proboterror/HIDman_ZX/firmware/usbhost.c

#include <stdio.h>
#include <stdlib.h>
#include <string.h>
#include "type.h"
#include "ch559.h"
#include "system.h"
#include "defs.h"
#include "usbdef.h"
#include "usbhost.h"
#include "data.h"
#include "settings.h"
#include "andyalloc.h"
#include "keyboardled.h"
#include "parsedescriptor.h"
#include "ps2protocol.h"
#include "usbll.h"
#include "preset.h"

#include "custom_handlers.h"
#include "kempston_joy.h"

#define RECEIVE_BUFFER_LEN 512
UINT8X ReceiveDataBuffer[RECEIVE_BUFFER_LEN];

__xdata bool DumpReport = 0;

void DumpHex(uint8_t *buffa, uint16_t len)
{
	static __xdata uint16_t cnt;

	for (cnt = 0; cnt < len; cnt++)
	{
		DEBUGOUT("%02X ", buffa[cnt]);
		if ((cnt & 0x000F) == 0x000F)
			DEBUGOUT("\n");
	}

	DEBUGOUT("\n\n");
}


void InitInterface(INTERFACE* Interface)
{
	memset(Interface, 0, sizeof(INTERFACE));

	Interface->InterfaceClass = USB_DEV_CLASS_RESERVED;
	Interface->InterfaceProtocol = USB_PROTOCOL_NONE;
	Interface->ReportSize = 0;
	Interface->EndpointNum = 0;


	for (int j = 0; j < MAX_ENDPOINT_NUM; j++)
	{
		Interface->Endpoint[j].EndpointAddr = 0;
		Interface->Endpoint[j].MaxPacketSize = 0;
		Interface->Endpoint[j].EndpointDir = ENDPOINT_IN;
		Interface->Endpoint[j].TOG = FALSE;
	}

	Interface->usesReports = 0;
}


void FillSetupReq(USB_SETUP_REQ *pSetupReq, UINT8 type, UINT8 req, UINT16 value, UINT16 index, UINT16 length)
{
	pSetupReq->bRequestType = type;
	pSetupReq->bRequest = req;
	pSetupReq->wValueL = value & 0xff;
	pSetupReq->wValueH = (value >> 8) & 0xff;
	pSetupReq->wIndexL = index & 0xff;
	pSetupReq->wIndexH = (index >> 8) & 0xff;
	pSetupReq->wLengthL = length & 0xff;
	pSetupReq->wLengthH = (length >> 8) & 0xff;
}

//-----------------------------------------------------------------------------------------
UINT8 GetDeviceDescr(USB_HUB_PORT *pUsbDevice, UINT8 *pDevDescr, UINT16 reqLen, UINT16 *pRetLen) //get device describtion
{
	static __xdata UINT8 s;
	static __xdata UINT16 len;

	static __xdata USB_SETUP_REQ SetupReq;
	FillSetupReq(&SetupReq, USB_REQ_TYP_IN | USB_REQ_TYP_STANDARD | USB_REQ_RECIP_DEVICE,
				 USB_GET_DESCRIPTOR, USB_DESCR_TYP_DEVICE << 8, 0, reqLen);

	s = HostCtrlTransfer(&SetupReq, pUsbDevice->MaxPacketSize0, pDevDescr, &len);

	if (s == ERR_SUCCESS)
	{
		if (pRetLen != NULL)
		{
			*pRetLen = len;
		}
	}

	return s;
}

//----------------------------------------------------------------------------------------
UINT8 GetConfigDescr(USB_HUB_PORT *pUsbDevice, UINT8 *pCfgDescr, UINT16 reqLen, UINT16 *pRetLen)
{
	static __xdata UINT8 s;
	static __xdata UINT16 len;

	static __xdata USB_SETUP_REQ SetupReq;
	FillSetupReq(&SetupReq, USB_REQ_TYP_IN | USB_REQ_TYP_STANDARD | USB_REQ_RECIP_DEVICE,
				 USB_GET_DESCRIPTOR, USB_DESCR_TYP_CONFIG << 8, 0, reqLen);
	s = HostCtrlTransfer(&SetupReq, pUsbDevice->MaxPacketSize0, pCfgDescr, &len);
	if (s == ERR_SUCCESS)
	{
		if (pRetLen != NULL)
		{
			*pRetLen = len;
		}
	}

	return s;
}

//-------------------------------------------------------------------------------------
UINT8 SetUsbAddress(USB_HUB_PORT *pUsbDevice, UINT8 addr)
{
	static __xdata UINT8 s;

	static __xdata USB_SETUP_REQ SetupReq;
	FillSetupReq(&SetupReq, USB_REQ_TYP_OUT | USB_REQ_TYP_STANDARD | USB_REQ_RECIP_DEVICE,
				 USB_SET_ADDRESS, addr, 0, 0);

	s = HostCtrlTransfer(&SetupReq, pUsbDevice->MaxPacketSize0, NULL, NULL);
	if (s == ERR_SUCCESS)
	{
		SetHostUsbAddr(addr);
	}

	return s;
}

//-------------------------------------------------------------------------------------
UINT8 SetUsbConfig(USB_HUB_PORT *pUsbDevice, UINT8 cfg)
{
	static __xdata UINT8 s;

	static __xdata USB_SETUP_REQ SetupReq;
	FillSetupReq(&SetupReq, USB_REQ_TYP_OUT | USB_REQ_TYP_STANDARD | USB_REQ_RECIP_DEVICE,
				 USB_SET_CONFIGURATION, cfg, 0, 0);

	s = HostCtrlTransfer(&SetupReq, pUsbDevice->MaxPacketSize0, NULL, NULL);

	return s;
}

//-----------------------------------------------------------------------------------------
UINT8 GetHubDescriptor(USB_HUB_PORT *pUsbDevice, UINT8 *pHubDescr, UINT16 reqLen, UINT16 *pRetLen)
{
	static __xdata UINT8 s;
	static __xdata UINT16 len;

	static __xdata USB_SETUP_REQ SetupReq;
	FillSetupReq(&SetupReq, USB_REQ_TYP_IN | USB_REQ_TYP_CLASS | USB_REQ_RECIP_DEVICE,
				 USB_GET_DESCRIPTOR, USB_DESCR_TYP_HUB << 8, 0, reqLen);
	s = HostCtrlTransfer(&SetupReq, pUsbDevice->MaxPacketSize0, (UINT8 *)pHubDescr, &len);

	if (s == ERR_SUCCESS)
	{
		if (pRetLen != NULL)
		{
			*pRetLen = len;
		}
	}

	return s;
}

//-----------------------------------------------------------------------------------------
UINT8 GetHubPortStatus(USB_HUB_PORT *pUsbDevice, UINT8 HubPort, UINT16 *pPortStatus, UINT16 *pPortChange)
{
	static __xdata UINT8 s;
	static __xdata UINT16 len;

	static __xdata UINT8 Ret[4];

	static __xdata USB_SETUP_REQ SetupReq;
	FillSetupReq(&SetupReq, USB_REQ_TYP_IN | USB_REQ_TYP_CLASS | USB_REQ_RECIP_OTHER,
				 USB_GET_STATUS, 0, HubPort, 4);

	s = HostCtrlTransfer(&SetupReq, pUsbDevice->MaxPacketSize0, Ret, &len);
	if (s == ERR_SUCCESS)
	{
		if (pPortStatus != NULL)
		{
			*pPortStatus = (Ret[1] << 8) | Ret[0];
		}

		if (pPortChange != NULL)
		{
			*pPortChange = (Ret[3] << 8) | Ret[2];
		}
	}

	return s;
}

//------------------------------------------------------------------------------------------
UINT8 SetHubPortFeature(USB_HUB_PORT *pUsbDevice, UINT8 HubPort, UINT8 selector) //this function set feature for port						//this funciton set
{
	static __xdata UINT8 s;

	static __xdata USB_SETUP_REQ SetupReq;
	FillSetupReq(&SetupReq, USB_REQ_TYP_OUT | USB_REQ_TYP_CLASS | USB_REQ_RECIP_OTHER,
				 USB_SET_FEATURE, selector, (0 << 8) | HubPort, 0);

	s = HostCtrlTransfer(&SetupReq, pUsbDevice->MaxPacketSize0, NULL, NULL);

	return s;
}

UINT8 ClearHubPortFeature(USB_HUB_PORT *pUsbDevice, UINT8 HubPort, UINT8 selector)
{
	static __xdata UINT8 s;

	static __xdata USB_SETUP_REQ SetupReq;
	FillSetupReq(&SetupReq, USB_REQ_TYP_OUT | USB_REQ_TYP_CLASS | USB_REQ_RECIP_OTHER,
				 USB_CLEAR_FEATURE, selector, (0 << 8) | HubPort, 0);

	s = HostCtrlTransfer(&SetupReq, pUsbDevice->MaxPacketSize0, NULL, NULL);

	return s;
}

//-----------------------------------------------------------------------------------------
UINT8 GetReportDescriptor(USB_HUB_PORT *pUsbDevice, UINT8 interface, UINT8 *pReportDescr, UINT16 reqLen, UINT16 *pRetLen)
{
	static __xdata UINT8 s;
	static __xdata UINT16 len;

	static __xdata USB_SETUP_REQ SetupReq;
	FillSetupReq(&SetupReq, USB_REQ_TYP_IN | USB_REQ_TYP_STANDARD | USB_REQ_RECIP_INTERF,
				 USB_GET_DESCRIPTOR, USB_DESCR_TYP_REPORT << 8, interface, reqLen);

	s = HostCtrlTransfer(&SetupReq, pUsbDevice->MaxPacketSize0, pReportDescr, &len);

	if (s == ERR_SUCCESS)
	{
		if (pRetLen != NULL)
		{
			*pRetLen = len;
		}
	}

	return s;
}

UINT8 SetBootProtocol(USB_HUB_PORT *pUsbDevice, UINT8 interface, uint16_t val)
{
	static __xdata UINT8 s;

	static __xdata USB_SETUP_REQ SetupReq;

	FillSetupReq(&SetupReq, 0b00100001, HID_SET_PROTOCOL, val, interface, 0);

	s = HostCtrlTransfer(&SetupReq, pUsbDevice->MaxPacketSize0, NULL, NULL);
	return s;
}

UINT8 GetBootProtocol(USB_HUB_PORT *pUsbDevice, UINT8 interface)
{
	static __xdata UINT8 s;
	static __xdata UINT8 ret;

	static __xdata USB_SETUP_REQ SetupReq;

	FillSetupReq(&SetupReq, 0b10100001, HID_GET_PROTOCOL, 0, interface, 1);

	s = HostCtrlTransfer(&SetupReq, pUsbDevice->MaxPacketSize0, &ret, NULL);

	return ret;
}

//-----------------------------------------------------------------------------------------
UINT8 SetIdle(USB_HUB_PORT *pUsbDevice, UINT16 durationMs, UINT8 reportID, UINT8 interface)
{
	static __xdata UINT8 s;

	static __xdata USB_SETUP_REQ SetupReq;
	UINT8 duration = (UINT8)(durationMs / 4);

	FillSetupReq(&SetupReq, USB_REQ_TYP_OUT | USB_REQ_TYP_CLASS | USB_REQ_RECIP_INTERF,
				 HID_SET_IDLE, (duration << 8) | reportID, interface, 0);

	s = HostCtrlTransfer(&SetupReq, pUsbDevice->MaxPacketSize0, NULL, NULL);

	return s;
}

//-----------------------------------------------------------------------------------------------
UINT8 SetReport(USB_HUB_PORT *pUsbDevice, UINT8 interface, UINT8 *pReport, UINT16 ReportLen)
{
	static __xdata UINT8 s;
	static __xdata UINT16 len;

	static __xdata USB_SETUP_REQ SetupReq;
	FillSetupReq(&SetupReq, USB_REQ_TYP_OUT | USB_REQ_TYP_CLASS | USB_REQ_RECIP_INTERF,
				 HID_SET_REPORT, HID_REPORT_OUTPUT << 8, interface, ReportLen);

	s = HostCtrlTransfer(&SetupReq, pUsbDevice->MaxPacketSize0, pReport, &len);

	return s;
}

//-----------------------------------------------------------------------------------------------
void InitUsbData(void)
{
	static int i;

	for (i = 0; i < ROOT_HUB_PORT_NUM; i++)
	{
		InitRootHubPortData(i);
	}
}

//-------------------------------------------------------------------------------------------
UINT8 HIDDataTransferReceive(USB_HUB_PORT *pUsbDevice)
{
	static UINT8 s, p;
	static int i, j;
	static int interfaceNum;
	static int endpointNum;

	static UINT16 len;

	custom_handler_t* hahdler = (custom_handler_t*)pUsbDevice->UserData;
	
	if (hahdler)
	{
		uint8_t gamepad_state = 0;

		if (hahdler->poll(pUsbDevice, &gamepad_state))
		{
			kempston_joy_set(gamepad_state);

			if(gamepad_state)
				setLED(false);
		}

		return ERR_SUCCESS;
	}

	s = 0;
	interfaceNum = pUsbDevice->InterfaceNum;
	for (i = 0; i < interfaceNum; i++)
	{
		//INTERFACE *pInterface = &pUsbDevice->Interface[i];
		__xdata INTERFACE *pInterface = (__xdata INTERFACE *)ListGetData(pUsbDevice->Interfaces, i);
		if (pInterface != NULL && pInterface->InterfaceClass == USB_DEV_CLASS_HID)
		{
			endpointNum = pInterface->EndpointNum;
			for (j = 0; j < endpointNum; j++)
			{
				ENDPOINT *pEndPoint = &pInterface->Endpoint[j];
				if (pEndPoint->EndpointDir == ENDPOINT_IN)
				{
					s = TransferReceive(pEndPoint, ReceiveDataBuffer, &len, 0);
					if (s == ERR_SUCCESS)
					{
						//TRACE1("interface %d data:", (UINT16)i);
						// HIS IS WHERE THE FUN STUFF GOES
						//ProcessHIDData(pInterface, ReceiveDataBuffer, len);
						ParseReport(pInterface, len * 8, ReceiveDataBuffer);
						if (HMSettings.SerialDebugOutput) {
							DEBUGOUT("I%hX L%X- ", i, len);
							DumpHex(ReceiveDataBuffer, len);
						}
					}
				}
			}
		}
	}

	return (s);
}

//enum device
BOOL EnumerateHubPort(__xdata USB_HUB_PORT *pUsbHubPort, UINT8 addr)
{
	static __xdata UINT8 s;
	static __xdata UINT16 len;
	static __xdata UINT16 cfgDescLen;

	static __xdata USB_HUB_PORT *pUsbDevice;
	static __xdata USB_CFG_DESCR *pCfgDescr;

	pUsbDevice = pUsbHubPort;

	//get first 8 bytes of device descriptor to get maxpacketsize0
	s = GetDeviceDescr(pUsbDevice, ReceiveDataBuffer, 8, &len);

	if (s != ERR_SUCCESS)
	{
		DEBUGOUT("gdd.fail\n");
		return (FALSE);
	}

	DEBUGOUT("gdd len:%d\n", len);

	ParseDeviceDescriptor((USB_DEV_DESCR *)ReceiveDataBuffer, len, pUsbDevice);

	DEBUGOUT("mps %d\n", pUsbDevice->MaxPacketSize0);

	//set device address
	s = SetUsbAddress(pUsbDevice, addr);
	if (s != ERR_SUCCESS)
	{
		DEBUGOUT("addr fail\n");
		return (FALSE);
	}

	DEBUGOUT("addr ok %d\n", pUsbDevice->DeviceAddress);
	pUsbDevice->DeviceAddress = addr;
	//get full bytes of device descriptor
	s = GetDeviceDescr(pUsbDevice, ReceiveDataBuffer, sizeof(USB_DEV_DESCR), &len);

	if (s != ERR_SUCCESS)
	{
		DEBUGOUT("gddfull fail\n");
		return (FALSE);
	}

	DEBUGOUT("gddfull ok %d\n", len);

	DEBUGOUT("Device Descriptor :\n")
	DumpHex(ReceiveDataBuffer, len);

	ParseDeviceDescriptor((USB_DEV_DESCR *)ReceiveDataBuffer, len, pUsbDevice);

	DEBUGOUT("0x%04X 0x%04X 0x%04X\n", pUsbDevice->VendorID, pUsbDevice->ProductID, pUsbDevice->bcdDevice);

	//get configure descriptor for the first time
	cfgDescLen = sizeof(USB_CFG_DESCR);

	s = GetConfigDescr(pUsbDevice, ReceiveDataBuffer, cfgDescLen, &len);
	if (s != ERR_SUCCESS)
	{
		DEBUGOUT("gcd1 fail\n");
		return (FALSE);
	}

	//get configure descriptor for the second time
	pCfgDescr = (USB_CFG_DESCR *)ReceiveDataBuffer;
	cfgDescLen = pCfgDescr->wTotalLengthL | (pCfgDescr->wTotalLengthH << 8);
	if (cfgDescLen > RECEIVE_BUFFER_LEN)
	{
		cfgDescLen = RECEIVE_BUFFER_LEN;
	}

	s = GetConfigDescr(pUsbDevice, ReceiveDataBuffer, cfgDescLen, &len);
	if (s != ERR_SUCCESS)
	{
		DEBUGOUT("gcd 2 fail\n");
		return (FALSE);
	}

	DEBUGOUT("Config Descriptor :\n")
	DumpHex(ReceiveDataBuffer, len);

	custom_handler_t* handler = match(pUsbDevice->VendorID, pUsbDevice->ProductID);

	if (handler)
	{
		pUsbHubPort->UserData = (void*)handler;
		handler->init(pUsbDevice, (USB_CFG_DESCR *)ReceiveDataBuffer, len);

		return true;
	}

	//parse config descriptor
	ParseConfigDescriptor((USB_CFG_DESCR *)ReceiveDataBuffer, len, pUsbDevice);

	DEBUGOUT("gcd ok %d\n", len);

	//set config
	s = SetUsbConfig(pUsbDevice, ((USB_CFG_DESCR *)ReceiveDataBuffer)->bConfigurationValue);
	if (s != ERR_SUCCESS)
	{
		DEBUGOUT("suc fail\n");
		return (FALSE);
	}

	TRACE("SetUsbConfig OK\r\n");
	TRACE1("configure=%bd\r\n", ((USB_CFG_DESCR *)ReceiveDataBuffer)->bConfigurationValue);

	TRACE1("pUsbDevice->InterfaceNum=%d\r\n", (UINT16)pUsbDevice->InterfaceNum);

	return (TRUE);
}

UINT8 AssignUniqueAddress(UINT8 RootHubIndex, UINT8 HubPortIndex)
{
	static UINT8 address;
	if (HubPortIndex == EXHUB_PORT_NONE)
	{
		address = (MAX_EXHUB_PORT_NUM + 1) * RootHubIndex + 1;
	}
	else
	{
		address = (MAX_EXHUB_PORT_NUM + 1) * RootHubIndex + 1 + HubPortIndex + 1;
	}

	return address;
}

BOOL EnumerateRootHubPort(UINT8 port)
{
	static __xdata UINT8 i, s;
	static __xdata UINT16 len;

	static __xdata UINT8 retry;

	static __xdata UINT8 addr;
	retry = 0;
	/*if (RootHubPort[port].HubPortStatus != PORT_DEVICE_INSERT)
	{
		return FALSE;
	}*/

	TRACE1("enumerate port:%bd\r\n", port);

//	DisableRootHubPort(port);

//	mDelaymS(500);

	ResetRootHubPort(port);
//	mDelaymS(500);

#if 1
	for (i = 0, s = 0; i < 10; i++) // 等待USB设备复位后重新连接,100mS超时
	{
		EnableRootHubPort(port);

		mDelaymS(1);
	}

#else
	for (i = 0, s = 0; i < 100; i++) // 等待USB设备复位后重新连接,100mS超时
	{
		mDelaymS(1);
		if (EnableRootHubPort(port) == ERR_SUCCESS) // 使能ROOT-HUB端口
		{
			i = 0;
			s++; // 计时等待USB设备连接后稳定
			if (s > 10 * retry)
			{
				break; // 已经稳定连接15mS
			}
		}
	}

	TRACE1("i:%d\r\n", (UINT16)i);

	if (i) // 复位后设备没有连接
	{
		DisableRootHubPort(port);
		TRACE1("Disable root hub %1d# port because of disconnect\n", (UINT16)port);

		return (ERR_USB_DISCON);
	}
#endif

	mDelaymS(100);

	SelectHubPort(port, EXHUB_PORT_NONE);

	addr = AssignUniqueAddress(port, EXHUB_PORT_NONE);
	if (EnumerateHubPort(&RootHubPort[port], addr))
	{
		RootHubPort[port].HubPortStatus = PORT_DEVICE_ENUM_SUCCESS;

		TRACE("EnumerateHubPort success\r\n");

		

		//SelectHubPort(port, EXHUB_PORT_NONE);
		if (RootHubPort[port].DeviceClass == USB_DEV_CLASS_HUB)
		{
			DEBUGOUT("\nFound hub\n");

			//hub
			USB_HUB_DESCR *pHubDescr;

			UINT8 hubPortNum;
			UINT16 hubPortStatus, hubPortChange;
			USB_HUB_PORT *pUsbDevice = &RootHubPort[port];

			//hub
			s = GetHubDescriptor(pUsbDevice, ReceiveDataBuffer, sizeof(USB_HUB_DESCR), &len);
			if (s != ERR_SUCCESS)
			{
				DisableRootHubPort(port);

				RootHubPort[port].HubPortStatus = PORT_DEVICE_ENUM_FAILED;
				DEBUGOUT("hub desc err\n");
				return (FALSE);
			}

			TRACE("GetHubDescriptor OK\r\n");
			TRACE1("len=%d\r\n", len);

			pHubDescr = (USB_HUB_DESCR *)ReceiveDataBuffer;
			hubPortNum = pHubDescr->bNbrPorts;

			TRACE1("hubPortNum=%bd\r\n", hubPortNum);
			DEBUGOUT("%d port hub\n", hubPortNum);

			if (hubPortNum > MAX_EXHUB_PORT_NUM)
			{
				hubPortNum = MAX_EXHUB_PORT_NUM;
			}

			pUsbDevice->HubPortNum = hubPortNum;

			//supply power for each port
			for (i = 0; i < hubPortNum; i++)
			{
				s = SetHubPortFeature(pUsbDevice, i + 1, HUB_PORT_POWER);
				if (s != ERR_SUCCESS)
				{
					TRACE1("SetHubPortFeature %d failed\r\n", (UINT16)i);

					SubHubPort[port][i].HubPortStatus = PORT_DEVICE_ENUM_FAILED;

					continue;
				}

				TRACE("SetHubPortFeature OK\r\n");
			}

			

			/*
			for (i = 0; i < hubPortNum; i++)
            {
                s = ClearHubPortFeature(pUsbDevice, i + 1, HUB_C_PORT_CONNECTION );
                if ( s != ERR_SUCCESS )
                {
                    TRACE1("ClearHubPortFeature %d failed\r\n", (UINT16)i);

                    continue;
                }

                TRACE("ClearHubPortFeature OK\r\n");
            }
*/
			INTERFACE *pInterface = (INTERFACE *)ListGetData(pUsbDevice->Interfaces, 0);

			ENDPOINT *pEndPoint = &pInterface->Endpoint[0];

			// "new thing" means wait for a change bitmap before clearing ports
			// this is how other USB stacks seem to do it
			printf("Doing new thing - %x\n", pInterface->Endpoint[0].EndpointAddr);

			uint8_t newthing = 1;

			s = TransferReceive(pEndPoint, ReceiveDataBuffer, &len, 20000);

			

			if (s != ERR_SUCCESS){
				DEBUGOUT("new enum. failed\n");
				// if "new thing" failed just clear all ports without waiting
				// seems to be required for some hubs
				newthing = 0;
				//return FALSE;
			}

			uint8_t changebitmap = ReceiveDataBuffer[0];

			DEBUGOUT("new enum. %x\n", changebitmap);

			for (i = 0; i < hubPortNum; i++)
			{
				if (!newthing || (changebitmap & (1 << (i+1)))) {
					DEBUGOUT("checkn port %d\n", i);
					mDelaymS(50);

					SelectHubPort(port, EXHUB_PORT_NONE); //切换到hub地址

					s = GetHubPortStatus(pUsbDevice, i + 1, &hubPortStatus, &hubPortChange);
					if (s != ERR_SUCCESS)
					{
						SubHubPort[port][i].HubPortStatus = PORT_DEVICE_ENUM_FAILED;

						TRACE1("GetHubPortStatus port:%d failed\r\n", (UINT16)(i + 1));

						return FALSE;
					}

					DEBUGOUT("ps- 0x%02X pc- 0x%02X\n", hubPortStatus, hubPortChange);

					TRACE2("hubPortStatus:0x%02X,hubPortChange:0x%02X\r\n", hubPortStatus, hubPortChange);

					if ((hubPortStatus & 0x0001) && (hubPortChange & 0x0001))
					{
						//device attached
						TRACE1("hubPort=%d\r\n", (UINT16)i);

						TRACE("device attached\r\n");

						DEBUGOUT("port %d attached\n", i);

						s = ClearHubPortFeature(pUsbDevice, i + 1, HUB_C_PORT_CONNECTION);
						if (s != ERR_SUCCESS)
						{
							SubHubPort[port][i].HubPortStatus = PORT_DEVICE_ENUM_FAILED;
							TRACE("ClearHubPortFeature failed\r\n");

							return FALSE;
						}

						TRACE("ClearHubPortFeature OK\r\n");


						s = SetHubPortFeature(pUsbDevice, i + 1, HUB_PORT_RESET); //reset the port device
						if (s != ERR_SUCCESS)
						{
							SubHubPort[port][i].HubPortStatus = PORT_DEVICE_ENUM_FAILED;

							TRACE1("SetHubPortFeature port:%d failed\r\n", (UINT16)(i + 1));

							return FALSE;
						}

						mDelaymS(100);
						do
						{
							s = GetHubPortStatus(pUsbDevice, i + 1, &hubPortStatus, &hubPortChange);
							if (s != ERR_SUCCESS)
							{
								SubHubPort[port][i].HubPortStatus = PORT_DEVICE_ENUM_FAILED;

								TRACE1("GetHubPortStatus port:%d failed\r\n", (UINT16)(i + 1));

								return FALSE;
							}

							mDelaymS(20);
						} while (hubPortStatus & 0x0010);

						if ((hubPortChange & 0x10) == 0x10) //reset over success
						{
							TRACE("reset complete\r\n");

							if (hubPortStatus & 0x0200)
							{
								//speed low
								SubHubPort[port][i].DeviceSpeed = LOW_SPEED;
								DEBUGOUT("lowspeed\n");
								TRACE("low speed device\r\n");
							}
							else
							{
								//full speed device
								SubHubPort[port][i].DeviceSpeed = FULL_SPEED;
								DEBUGOUT("fullspeed\n");
								TRACE("full speed device\r\n");
							}

							s = ClearHubPortFeature(pUsbDevice, i + 1, HUB_C_PORT_RESET);
							if (s != ERR_SUCCESS)
							{
								TRACE("ClearHubPortFeature failed\r\n");
							}
							else
							{
								TRACE("ClearHubPortFeature OK\r\n");
							}

							/*s = ClearHubPortFeature(pUsbDevice, i + 1, HUB_PORT_SUSPEND);
							if (s != ERR_SUCCESS)
							{
								SubHubPort[port][i].HubPortStatus = PORT_DEVICE_ENUM_FAILED;
								TRACE("ClearHubPortFeature failed\r\n");

								return FALSE;
							}

							TRACE("ClearHubPortFeature OK\r\n");

							mDelaymS(500);*/

							SelectHubPort(port, i);

							addr = AssignUniqueAddress(port, i);
							if (EnumerateHubPort(&SubHubPort[port][i], addr))
							{
								DEBUGOUT("enum.OK\n");
								TRACE("EnumerateHubPort success\r\n");
								SubHubPort[port][i].HubPortStatus = PORT_DEVICE_ENUM_SUCCESS;
							}
							else
							{
								DEBUGOUT("enum.fail\n");
								TRACE("EnumerateHubPort failed\r\n");
								SubHubPort[port][i].HubPortStatus = PORT_DEVICE_ENUM_FAILED;
							}
						}
					}
				}
			}
		}
	}
	else
	{
		DisableRootHubPort(port);

		RootHubPort[port].HubPortStatus = PORT_DEVICE_ENUM_FAILED;
	}

	return TRUE;
}

UINT8 QueryHubPortAttach(void)
{
	static __xdata BOOL res;

	static __xdata UINT8 s;

	res = FALSE; s = ERR_SUCCESS;

	if (UIF_DETECT)
	{
		//plug in or plug out
		UIF_DETECT = 0;

		if (USB_HUB_ST & bUHS_H0_ATTACH)
		{
			//port 0 plug in
			if (RootHubPort[0].HubPortStatus == PORT_DEVICE_NONE
				/*|| (UHUB0_CTRL & bUH_PORT_EN) == 0x00*/)
			{
				DisableRootHubPort(0);

				RootHubPort[0].HubPortStatus = PORT_DEVICE_INSERT;

				s = ERR_USB_CONNECT;

				TRACE("hub 0 dev in\r\n");
			}
		}
		else if (RootHubPort[0].HubPortStatus >= PORT_DEVICE_INSERT)
		{
			DisableRootHubPort(0);

			if (s == ERR_SUCCESS)
			{
				s = ERR_USB_DISCON;
			}

			TRACE("hub 0 dev out\r\n");
		}

		if (USB_HUB_ST & bUHS_H1_ATTACH)
		{
			//port 1 plug in
			if (RootHubPort[1].HubPortStatus == PORT_DEVICE_NONE
				/*|| ( UHUB1_CTRL & bUH_PORT_EN ) == 0x00*/)
			{
				DisableRootHubPort(1);

				RootHubPort[1].HubPortStatus = PORT_DEVICE_INSERT;

				s = ERR_USB_CONNECT;

				TRACE("hub 1 dev in\r\n");
			}
		}
		else if (RootHubPort[1].HubPortStatus >= PORT_DEVICE_INSERT)
		{
			DisableRootHubPort(1);

			if (s == ERR_SUCCESS)
			{
				s = ERR_USB_DISCON;
			}

			TRACE("hub 1 dev out\r\n");
		}
	}

	return s;
}


void regrabinterfaces(__xdata USB_HUB_PORT *pUsbHubPort)
{
	static __xdata UINT8 i, s, c;
	static __xdata UINT16 len, cnt;
	static __xdata USB_HUB_PORT *pUsbDevice;

	pUsbDevice = pUsbHubPort;
	if (pUsbDevice->DeviceClass != USB_DEV_CLASS_HUB)
	{
		for (i = 0; i < pUsbDevice->InterfaceNum; i++)
		{
#ifdef DEBUG
			int j;
#endif

			DEBUGOUT("\n\n");
			//INTERFACE *pInterface = &pUsbDevice->Interface[i];		
			INTERFACE *pInterface = (INTERFACE *)ListGetData(pUsbDevice->Interfaces, i);

			TRACE1("InterfaceClass=0x%02X\r\n", (UINT16)pInterface->InterfaceClass);
			TRACE1("InterfaceProtocol=0x%02X\r\n", (UINT16)pInterface->InterfaceProtocol);

			if (pInterface->InterfaceClass == USB_DEV_CLASS_HID)
			{
				s = SetIdle(pUsbDevice, 0, 0, i);

				if (s != ERR_SUCCESS)
				{
					TRACE("SetIdle failed\r\n");
				}
				else
				{
					TRACE("SetIdle OK\r\n");
				}

				DEBUGOUT("Interface %x:\n", i);
				DEBUGOUT("InterfaceProtocol: %x\r\n", pInterface->InterfaceProtocol);

				TRACE1("Report Size:%d\r\n", pInterface->ReportSize);
				s = GetReportDescriptor(pUsbDevice, i, ReceiveDataBuffer, pInterface->ReportSize <= sizeof(ReceiveDataBuffer) ? pInterface->ReportSize : sizeof(ReceiveDataBuffer), &len);

				if (s != ERR_SUCCESS)
				{
					DEBUGOUT("rep descr fail %u\n", s);
					return; // FALSE;
				}

				TRACE("GetReportDescriptor OK\r\n");
				TRACE1("get report descr len:%d\r\n", len);

				DEBUGOUT("\n\nInterface %hx Report Descriptor - \n", i);
				DumpHex(ReceiveDataBuffer, len);



				// use default boot mode descriptors if a keyboard or mouse is detected and "advanced USB" is disabled in menu
				if (
					(!HMSettings.MouseReportMode && pInterface->InterfaceProtocol == HID_PROTOCOL_MOUSE) ||
					(!HMSettings.KeyboardReportMode && pInterface->InterfaceProtocol == HID_PROTOCOL_KEYBOARD)
					)
				{
					// if it supports boot mode, enable that and use the default descriptor
					if (pInterface->InterfaceSubClass == 0x01) {
						DEBUGOUT("set boot mode - %x - ", GetBootProtocol(pUsbDevice, i));
						SetBootProtocol(pUsbDevice, i, 0);
						ParseReportDescriptor(
							pInterface->InterfaceProtocol == HID_PROTOCOL_MOUSE ? StandardMouseDescriptor : StandardKeyboardDescriptor, 
							pInterface->InterfaceProtocol == HID_PROTOCOL_MOUSE ? 50 : 63, 
							pInterface
						);
						
						DEBUGOUT("%x\n", GetBootProtocol(pUsbDevice, i));
					}
					// Otherwise don't attempt to use this device at all unless advanced USB is enabled
					else{ 
						DEBUGOUT("No boot mode\n");
						continue;
					}
				}
				else {
					// only switch into report mode if boot mode is supported (yeah that's the way it works)
					if (pInterface->InterfaceSubClass == 0x01) {
						DEBUGOUT("set report mode - %x - ", GetBootProtocol(pUsbDevice, i));
						SetBootProtocol(pUsbDevice, i, 1);
						DEBUGOUT("%x\n", GetBootProtocol(pUsbDevice, i));
					}
					
					ParseReportDescriptor(ReceiveDataBuffer, len, pInterface);
					DumpHID(pInterface);
				}

				if (pInterface->InterfaceProtocol == HID_PROTOCOL_KEYBOARD)
				{
					UINT8 led;

					led = GetKeyboardLedStatus();
					SetReport(pUsbDevice, i, &led, sizeof(led));
					DEBUGOUT("SetReport\n");
				}
			}
		}
	}
}

void RegrabDeviceReports(UINT8 port)
{
	static __xdata USB_HUB_PORT *pUsbHubPort;
	pUsbHubPort = &RootHubPort[port];

	if (pUsbHubPort->HubPortStatus == PORT_DEVICE_ENUM_SUCCESS)
	{
		if (pUsbHubPort->DeviceClass != USB_DEV_CLASS_HUB)
		{
			SelectHubPort(port, EXHUB_PORT_NONE);
			regrabinterfaces(pUsbHubPort);
		}
		else
		{
			UINT8 exHubPortNum = pUsbHubPort->HubPortNum;
			UINT8 i;

			for (i = 0; i < exHubPortNum; i++)
			{
				pUsbHubPort = &SubHubPort[port][i];

				if (pUsbHubPort->HubPortStatus == PORT_DEVICE_ENUM_SUCCESS && pUsbHubPort->DeviceClass != USB_DEV_CLASS_HUB)
				{
					SelectHubPort(port, i);
					regrabinterfaces(pUsbHubPort);
				}
			}
		}
	}
}

void ReenumerateAllPorts(void){
	UINT8 i;
	
	DEBUGOUT("reenumerating all ports\n");
	mDelaymS(150);

	InitUsbData();
	andyclearmem();
	InitPresets();
	
	for (i = 0; i < ROOT_HUB_PORT_NUM; i++)
	{
		DEBUGOUT("port %d\n", i);

		EnumerateRootHubPort(i);
		RegrabDeviceReports(i);
	}
	DEBUGOUT("done reenumerating\n");
}

//----------------------------------------------------------------------------------
void DealUsbPort(void) //main function should use it at least 500ms
{
	static __xdata UINT8 s;

	s = QueryHubPortAttach();
	if (s == ERR_USB_CONNECT)
	{
		ReenumerateAllPorts();
	}
}

void InterruptProcessRootHubPort(UINT8 port)
{
	static __xdata USB_HUB_PORT *pUsbHubPort;
	pUsbHubPort = &RootHubPort[port];

	if (pUsbHubPort->HubPortStatus == PORT_DEVICE_ENUM_SUCCESS)
	{
		if (pUsbHubPort->DeviceClass != USB_DEV_CLASS_HUB)
		{
			SelectHubPort(port, EXHUB_PORT_NONE);

			HIDDataTransferReceive(pUsbHubPort);
			
		}
		else
		{
			UINT8 exHubPortNum = pUsbHubPort->HubPortNum;
			UINT8 i;

			for (i = 0; i < exHubPortNum; i++)
			{
				pUsbHubPort = &SubHubPort[port][i];

				if (pUsbHubPort->HubPortStatus == PORT_DEVICE_ENUM_SUCCESS && pUsbHubPort->DeviceClass != USB_DEV_CLASS_HUB)
				{
					SelectHubPort(port, i);
					HIDDataTransferReceive(pUsbHubPort);
				}
			}
		}
	}
}

void UpdateUsbKeyboardLedInternal(USB_HUB_PORT *pUsbDevice, UINT8 led)
{
	UINT8 i;
	for (i = 0; i < pUsbDevice->InterfaceNum; i++)
	{
		//INTERFACE *pInterface = &pUsbDevice->Interface[i];
		INTERFACE *pInterface = (INTERFACE *)ListGetData(pUsbDevice->Interfaces, i);
		if (pInterface->InterfaceClass == USB_DEV_CLASS_HID)
		{
			if (pInterface->InterfaceProtocol == HID_PROTOCOL_KEYBOARD)
			{
				SetReport(pUsbDevice, i, &led, 1);

				TRACE1("led=0x%x\r\n", led);
			}
		}
	}
}

//-----------------------------------------------------------------------------
void UpdateUsbKeyboardLed(UINT8 led)
{
	UINT8 i, j;

	for (i = 0; i < ROOT_HUB_PORT_NUM; i++)
	{
		USB_HUB_PORT *pUsbHubPort = &RootHubPort[i];
		if (pUsbHubPort->HubPortStatus == PORT_DEVICE_ENUM_SUCCESS)
		{
			if (pUsbHubPort->DeviceClass != USB_DEV_CLASS_HUB)
			{
				SelectHubPort(i, EXHUB_PORT_NONE);

				UpdateUsbKeyboardLedInternal(pUsbHubPort, led);
			}
			else
			{
				int exHubPortNum = pUsbHubPort->HubPortNum;

				for (j = 0; j < exHubPortNum; j++)
				{
					pUsbHubPort = &SubHubPort[i][j];

					if (pUsbHubPort->HubPortStatus == PORT_DEVICE_ENUM_SUCCESS && pUsbHubPort->DeviceClass != USB_DEV_CLASS_HUB)
					{
						SelectHubPort(i, j);

						UpdateUsbKeyboardLedInternal(pUsbHubPort, led);
					}
				}
			}
		}
	}
}

__xdata BOOL volatile s_CheckUsbPort0 = FALSE;
__xdata BOOL volatile s_CheckUsbPort1 = FALSE;

void ProcessUsbHostPort(void)
{	

	DealUsbPort();
	if (s_CheckUsbPort0)
	{
		s_CheckUsbPort0 = FALSE;
		
		InterruptProcessRootHubPort(0);
	}
	if (s_CheckUsbPort1)
	{
		s_CheckUsbPort1 = FALSE;

		InterruptProcessRootHubPort(1);
	}
}
