proboterror/HIDman_ZX/firmware/scancode.c

#include<stdio.h>
#ifndef __SDCC
#define __code
#endif
__code unsigned char KEY_SET2_PWR_MAKE[] = { 0x02, 0xE0, 0x37, };
__code unsigned char KEY_SET2_PWR_BREAK[] = { 0x03, 0xE0, 0xF0, 0x37, };

__code unsigned char KEY_SET2_SLEP_MAKE[] = { 0x02, 0xE0, 0x3F, };
__code unsigned char KEY_SET2_SLEP_BREAK[] = { 0x03, 0xE0, 0xF0, 0x3F, };

__code unsigned char KEY_SET2_WAKE_MAKE[] = { 0x02, 0xE0, 0x5E, };
__code unsigned char KEY_SET2_WAKE_BREAK[] = { 0x03, 0xE0, 0xF0, 0x5E, };

__code unsigned char KEY_SET2_A_MAKE[] = { 0x01, 0x1C, };
__code unsigned char KEY_SET2_A_BREAK[] = { 0x02, 0xF0, 0x1C, };

__code unsigned char KEY_SET2_B_MAKE[] = { 0x01, 0x32, };
__code unsigned char KEY_SET2_B_BREAK[] = { 0x02, 0xF0, 0x32, };

__code unsigned char KEY_SET2_C_MAKE[] = { 0x01, 0x21, };
__code unsigned char KEY_SET2_C_BREAK[] = { 0x02, 0xF0, 0x21, };

__code unsigned char KEY_SET2_D_MAKE[] = { 0x01, 0x23, };
__code unsigned char KEY_SET2_D_BREAK[] = { 0x02, 0xF0, 0x23, };

__code unsigned char KEY_SET2_E_MAKE[] = { 0x01, 0x24, };
__code unsigned char KEY_SET2_E_BREAK[] = { 0x02, 0xF0, 0x24, };

__code unsigned char KEY_SET2_F_MAKE[] = { 0x01, 0x2B, };
__code unsigned char KEY_SET2_F_BREAK[] = { 0x02, 0xF0, 0x2B, };

__code unsigned char KEY_SET2_G_MAKE[] = { 0x01, 0x34, };
__code unsigned char KEY_SET2_G_BREAK[] = { 0x02, 0xF0, 0x34, };

__code unsigned char KEY_SET2_H_MAKE[] = { 0x01, 0x33, };
__code unsigned char KEY_SET2_H_BREAK[] = { 0x02, 0xF0, 0x33, };

__code unsigned char KEY_SET2_I_MAKE[] = { 0x01, 0x43, };
__code unsigned char KEY_SET2_I_BREAK[] = { 0x02, 0xF0, 0x43, };

__code unsigned char KEY_SET2_J_MAKE[] = { 0x01, 0x3B, };
__code unsigned char KEY_SET2_J_BREAK[] = { 0x02, 0xF0, 0x3B, };

__code unsigned char KEY_SET2_K_MAKE[] = { 0x01, 0x42, };
__code unsigned char KEY_SET2_K_BREAK[] = { 0x02, 0xF0, 0x42, };

__code unsigned char KEY_SET2_L_MAKE[] = { 0x01, 0x4B, };
__code unsigned char KEY_SET2_L_BREAK[] = { 0x02, 0xF0, 0x4B, };

__code unsigned char KEY_SET2_M_MAKE[] = { 0x01, 0x3A, };
__code unsigned char KEY_SET2_M_BREAK[] = { 0x02, 0xF0, 0x3A, };

__code unsigned char KEY_SET2_N_MAKE[] = { 0x01, 0x31, };
__code unsigned char KEY_SET2_N_BREAK[] = { 0x02, 0xF0, 0x31, };

__code unsigned char KEY_SET2_O_MAKE[] = { 0x01, 0x44, };
__code unsigned char KEY_SET2_O_BREAK[] = { 0x02, 0xF0, 0x44, };

__code unsigned char KEY_SET2_P_MAKE[] = { 0x01, 0x4D, };
__code unsigned char KEY_SET2_P_BREAK[] = { 0x02, 0xF0, 0x4D, };

__code unsigned char KEY_SET2_Q_MAKE[] = { 0x01, 0x15, };
__code unsigned char KEY_SET2_Q_BREAK[] = { 0x02, 0xF0, 0x15, };

__code unsigned char KEY_SET2_R_MAKE[] = { 0x01, 0x2D, };
__code unsigned char KEY_SET2_R_BREAK[] = { 0x02, 0xF0, 0x2D, };

__code unsigned char KEY_SET2_S_MAKE[] = { 0x01, 0x1B, };
__code unsigned char KEY_SET2_S_BREAK[] = { 0x02, 0xF0, 0x1B, };

__code unsigned char KEY_SET2_T_MAKE[] = { 0x01, 0x2C, };
__code unsigned char KEY_SET2_T_BREAK[] = { 0x02, 0xF0, 0x2C, };

__code unsigned char KEY_SET2_U_MAKE[] = { 0x01, 0x3C, };
__code unsigned char KEY_SET2_U_BREAK[] = { 0x02, 0xF0, 0x3C, };

__code unsigned char KEY_SET2_V_MAKE[] = { 0x01, 0x2A, };
__code unsigned char KEY_SET2_V_BREAK[] = { 0x02, 0xF0, 0x2A, };

__code unsigned char KEY_SET2_W_MAKE[] = { 0x01, 0x1D, };
__code unsigned char KEY_SET2_W_BREAK[] = { 0x02, 0xF0, 0x1D, };

__code unsigned char KEY_SET2_X_MAKE[] = { 0x01, 0x22, };
__code unsigned char KEY_SET2_X_BREAK[] = { 0x02, 0xF0, 0x22, };

__code unsigned char KEY_SET2_Y_MAKE[] = { 0x01, 0x35, };
__code unsigned char KEY_SET2_Y_BREAK[] = { 0x02, 0xF0, 0x35, };

__code unsigned char KEY_SET2_Z_MAKE[] = { 0x01, 0x1A, };
__code unsigned char KEY_SET2_Z_BREAK[] = { 0x02, 0xF0, 0x1A, };

__code unsigned char KEY_SET2_1_MAKE[] = { 0x01, 0x16, };
__code unsigned char KEY_SET2_1_BREAK[] = { 0x02, 0xF0, 0x16, };

__code unsigned char KEY_SET2_2_MAKE[] = { 0x01, 0x1E, };
__code unsigned char KEY_SET2_2_BREAK[] = { 0x02, 0xF0, 0x1E, };

__code unsigned char KEY_SET2_3_MAKE[] = { 0x01, 0x26, };
__code unsigned char KEY_SET2_3_BREAK[] = { 0x02, 0xF0, 0x26, };

__code unsigned char KEY_SET2_4_MAKE[] = { 0x01, 0x25, };
__code unsigned char KEY_SET2_4_BREAK[] = { 0x02, 0xF0, 0x25, };

__code unsigned char KEY_SET2_5_MAKE[] = { 0x01, 0x2E, };
__code unsigned char KEY_SET2_5_BREAK[] = { 0x02, 0xF0, 0x2E, };

__code unsigned char KEY_SET2_6_MAKE[] = { 0x01, 0x36, };
__code unsigned char KEY_SET2_6_BREAK[] = { 0x02, 0xF0, 0x36, };

__code unsigned char KEY_SET2_7_MAKE[] = { 0x01, 0x3D, };
__code unsigned char KEY_SET2_7_BREAK[] = { 0x02, 0xF0, 0x3D, };

__code unsigned char KEY_SET2_8_MAKE[] = { 0x01, 0x3E, };
__code unsigned char KEY_SET2_8_BREAK[] = { 0x02, 0xF0, 0x3E, };

__code unsigned char KEY_SET2_9_MAKE[] = { 0x01, 0x46, };
__code unsigned char KEY_SET2_9_BREAK[] = { 0x02, 0xF0, 0x46, };

__code unsigned char KEY_SET2_0_MAKE[] = { 0x01, 0x45, };
__code unsigned char KEY_SET2_0_BREAK[] = { 0x02, 0xF0, 0x45, };

__code unsigned char KEY_SET2_ENTER_MAKE[] = { 0x01, 0x5A, };
__code unsigned char KEY_SET2_ENTER_BREAK[] = { 0x02, 0xF0, 0x5A, };

__code unsigned char KEY_SET2_ESCAPE_MAKE[] = { 0x01, 0x76, };
__code unsigned char KEY_SET2_ESCAPE_BREAK[] = { 0x02, 0xF0, 0x76, };

__code unsigned char KEY_SET2_BKSPACE_MAKE[] = { 0x01, 0x66, };
__code unsigned char KEY_SET2_BKSPACE_BREAK[] = { 0x02, 0xF0, 0x66, };

__code unsigned char KEY_SET2_TAB_MAKE[] = { 0x01, 0x0D, };
__code unsigned char KEY_SET2_TAB_BREAK[] = { 0x02, 0xF0, 0x0D, };

__code unsigned char KEY_SET2_SPACE_MAKE[] = { 0x01, 0x29, };
__code unsigned char KEY_SET2_SPACE_BREAK[] = { 0x02, 0xF0, 0x29, };

__code unsigned char KEY_SET2_DASH_MAKE[] = { 0x01, 0x4E, };
__code unsigned char KEY_SET2_DASH_BREAK[] = { 0x02, 0xF0, 0x4E, };

__code unsigned char KEY_SET2_EQUALS_MAKE[] = { 0x01, 0x55, };
__code unsigned char KEY_SET2_EQUALS_BREAK[] = { 0x02, 0xF0, 0x55, };

__code unsigned char KEY_SET2_LEFTSQB_MAKE[] = { 0x01, 0x54, };
__code unsigned char KEY_SET2_LEFTSQB_BREAK[] = { 0x02, 0xF0, 0x54, };

__code unsigned char KEY_SET2_RIGHTSQB_MAKE[] = { 0x01, 0x5B, };
__code unsigned char KEY_SET2_RIGHTSQB_BREAK[] = { 0x02, 0xF0, 0x5B, };

__code unsigned char KEY_SET2_BKSLASH_MAKE[] = { 0x01, 0x5D, };
__code unsigned char KEY_SET2_BKSLASH_BREAK[] = { 0x02, 0xF0, 0x5D, };

__code unsigned char KEY_SET2_EURO1_MAKE[] = { 0x01, 0x5D, };
__code unsigned char KEY_SET2_EURO1_BREAK[] = { 0x02, 0xF0, 0x5D, };

__code unsigned char KEY_SET2_SEMICOLON_MAKE[] = { 0x01, 0x4C, };
__code unsigned char KEY_SET2_SEMICOLON_BREAK[] = { 0x02, 0xF0, 0x4C, };

__code unsigned char KEY_SET2_APOSTROPHE_MAKE[] = { 0x01, 0x52, };
__code unsigned char KEY_SET2_APOSTROPHE_BREAK[] = { 0x02, 0xF0, 0x52, };

__code unsigned char KEY_SET2_TILDE_MAKE[] = { 0x01, 0x0E, };
__code unsigned char KEY_SET2_TILDE_BREAK[] = { 0x02, 0xF0, 0x0E, };

__code unsigned char KEY_SET2_COMMA_MAKE[] = { 0x01, 0x41, };
__code unsigned char KEY_SET2_COMMA_BREAK[] = { 0x02, 0xF0, 0x41, };

__code unsigned char KEY_SET2_PERIOD_MAKE[] = { 0x01, 0x49, };
__code unsigned char KEY_SET2_PERIOD_BREAK[] = { 0x02, 0xF0, 0x49, };

__code unsigned char KEY_SET2_FWSLASH_MAKE[] = { 0x01, 0x4A, };
__code unsigned char KEY_SET2_FWSLASH_BREAK[] = { 0x02, 0xF0, 0x4A, };

__code unsigned char KEY_SET2_CAPS_MAKE[] = { 0x01, 0x58, };
__code unsigned char KEY_SET2_CAPS_BREAK[] = { 0x02, 0xF0, 0x58, };

__code unsigned char KEY_SET2_F1_MAKE[] = { 0x01, 0x05, };
__code unsigned char KEY_SET2_F1_BREAK[] = { 0x02, 0xF0, 0x05, };

__code unsigned char KEY_SET2_F2_MAKE[] = { 0x01, 0x06, };
__code unsigned char KEY_SET2_F2_BREAK[] = { 0x02, 0xF0, 0x06, };

__code unsigned char KEY_SET2_F3_MAKE[] = { 0x01, 0x04, };
__code unsigned char KEY_SET2_F3_BREAK[] = { 0x02, 0xF0, 0x04, };

__code unsigned char KEY_SET2_F4_MAKE[] = { 0x01, 0x0C, };
__code unsigned char KEY_SET2_F4_BREAK[] = { 0x02, 0xF0, 0x0C, };

__code unsigned char KEY_SET2_F5_MAKE[] = { 0x01, 0x03, };
__code unsigned char KEY_SET2_F5_BREAK[] = { 0x02, 0xF0, 0x03, };

__code unsigned char KEY_SET2_F6_MAKE[] = { 0x01, 0x0B, };
__code unsigned char KEY_SET2_F6_BREAK[] = { 0x02, 0xF0, 0x0B, };

__code unsigned char KEY_SET2_F7_MAKE[] = { 0x01, 0x83, };
__code unsigned char KEY_SET2_F7_BREAK[] = { 0x02, 0xF0, 0x83, };

__code unsigned char KEY_SET2_F8_MAKE[] = { 0x01, 0x0A, };
__code unsigned char KEY_SET2_F8_BREAK[] = { 0x02, 0xF0, 0x0A, };

__code unsigned char KEY_SET2_F9_MAKE[] = { 0x01, 0x01, };
__code unsigned char KEY_SET2_F9_BREAK[] = { 0x02, 0xF0, 0x01, };

__code unsigned char KEY_SET2_F10_MAKE[] = { 0x01, 0x09, };
__code unsigned char KEY_SET2_F10_BREAK[] = { 0x02, 0xF0, 0x09, };

__code unsigned char KEY_SET2_F11_MAKE[] = { 0x01, 0x78, };
__code unsigned char KEY_SET2_F11_BREAK[] = { 0x02, 0xF0, 0x78, };

__code unsigned char KEY_SET2_F12_MAKE[] = { 0x01, 0x07, };
__code unsigned char KEY_SET2_F12_BREAK[] = { 0x02, 0xF0, 0x07, };

__code unsigned char KEY_SET2_PRTSCR_MAKE[] = { 0x02, 0xE0, 0x7C, };
__code unsigned char KEY_SET2_PRTSCR_BREAK[] = { 0x03, 0xE0, 0xF0, 0x7C, };

__code unsigned char KEY_SET2_SCRLOCK_MAKE[] = { 0x01, 0x7E, };
__code unsigned char KEY_SET2_SCRLOCK_BREAK[] = { 0x02, 0xF0, 0x7E, };

__code unsigned char KEY_SET2_PAUSE_MAKE[] = { 0x08, 0xE1, 0x14, 0x77, 0xE1, 0xF0, 0x14, 0xF0, 0x77, };
__code unsigned char KEY_SET2_INSERT_MAKE[] = { 0x02, 0xE0, 0x70, };
__code unsigned char KEY_SET2_INSERT_BREAK[] = { 0x03, 0xE0, 0xF0, 0x70, };

__code unsigned char KEY_SET2_HOME_MAKE[] = { 0x02, 0xE0, 0x6C, };
__code unsigned char KEY_SET2_HOME_BREAK[] = { 0x03, 0xE0, 0xF0, 0x6C, };

__code unsigned char KEY_SET2_PGUP_MAKE[] = { 0x02, 0xE0, 0x7D, };
__code unsigned char KEY_SET2_PGUP_BREAK[] = { 0x03, 0xE0, 0xF0, 0x7D, };

__code unsigned char KEY_SET2_DELETE_MAKE[] = { 0x02, 0xE0, 0x71, };
__code unsigned char KEY_SET2_DELETE_BREAK[] = { 0x03, 0xE0, 0xF0, 0x71, };

__code unsigned char KEY_SET2_END_MAKE[] = { 0x02, 0xE0, 0x69, };
__code unsigned char KEY_SET2_END_BREAK[] = { 0x03, 0xE0, 0xF0, 0x69, };

__code unsigned char KEY_SET2_PGDN_MAKE[] = { 0x02, 0xE0, 0x7A, };
__code unsigned char KEY_SET2_PGDN_BREAK[] = { 0x03, 0xE0, 0xF0, 0x7A, };

__code unsigned char KEY_SET2_RIGHT_MAKE[] = { 0x02, 0xE0, 0x74, };
__code unsigned char KEY_SET2_RIGHT_BREAK[] = { 0x03, 0xE0, 0xF0, 0x74, };

__code unsigned char KEY_SET2_LEFT_MAKE[] = { 0x02, 0xE0, 0x6B, };
__code unsigned char KEY_SET2_LEFT_BREAK[] = { 0x03, 0xE0, 0xF0, 0x6B, };

__code unsigned char KEY_SET2_DOWN_MAKE[] = { 0x02, 0xE0, 0x72, };
__code unsigned char KEY_SET2_DOWN_BREAK[] = { 0x03, 0xE0, 0xF0, 0x72, };

__code unsigned char KEY_SET2_UP_MAKE[] = { 0x02, 0xE0, 0x75, };
__code unsigned char KEY_SET2_UP_BREAK[] = { 0x03, 0xE0, 0xF0, 0x75, };

__code unsigned char KEY_SET2_NUMLCK_MAKE[] = { 0x01, 0x77, };
__code unsigned char KEY_SET2_NUMLCK_BREAK[] = { 0x02, 0xF0, 0x77, };

__code unsigned char KEY_SET2_PADFWSLASH_MAKE[] = { 0x02, 0xE0, 0x4A, };
__code unsigned char KEY_SET2_PADFWSLASH_BREAK[] = { 0x03, 0xE0, 0xF0, 0x4A, };

__code unsigned char KEY_SET2_PADASTERISK_MAKE[] = { 0x01, 0x7C, };
__code unsigned char KEY_SET2_PADASTERISK_BREAK[] = { 0x02, 0xF0, 0x7C, };

__code unsigned char KEY_SET2_PADMINUS_MAKE[] = { 0x01, 0x7B, };
__code unsigned char KEY_SET2_PADMINUS_BREAK[] = { 0x02, 0xF0, 0x7B, };

__code unsigned char KEY_SET2_PADPLUS_MAKE[] = { 0x01, 0x79, };
__code unsigned char KEY_SET2_PADPLUS_BREAK[] = { 0x02, 0xF0, 0x79, };

__code unsigned char KEY_SET2_PADENTER_MAKE[] = { 0x02, 0xE0, 0x5A, };
__code unsigned char KEY_SET2_PADENTER_BREAK[] = { 0x03, 0xE0, 0xF0, 0x5A, };

__code unsigned char KEY_SET2_PAD1_MAKE[] = { 0x01, 0x69, };
__code unsigned char KEY_SET2_PAD1_BREAK[] = { 0x02, 0xF0, 0x69, };

__code unsigned char KEY_SET2_PAD2_MAKE[] = { 0x01, 0x72, };
__code unsigned char KEY_SET2_PAD2_BREAK[] = { 0x02, 0xF0, 0x72, };

__code unsigned char KEY_SET2_PAD3_MAKE[] = { 0x01, 0x7A, };
__code unsigned char KEY_SET2_PAD3_BREAK[] = { 0x02, 0xF0, 0x7A, };

__code unsigned char KEY_SET2_PAD4_MAKE[] = { 0x01, 0x6B, };
__code unsigned char KEY_SET2_PAD4_BREAK[] = { 0x02, 0xF0, 0x6B, };

__code unsigned char KEY_SET2_PAD5_MAKE[] = { 0x01, 0x73, };
__code unsigned char KEY_SET2_PAD5_BREAK[] = { 0x02, 0xF0, 0x73, };

__code unsigned char KEY_SET2_PAD6_MAKE[] = { 0x01, 0x74, };
__code unsigned char KEY_SET2_PAD6_BREAK[] = { 0x02, 0xF0, 0x74, };

__code unsigned char KEY_SET2_PAD7_MAKE[] = { 0x01, 0x6C, };
__code unsigned char KEY_SET2_PAD7_BREAK[] = { 0x02, 0xF0, 0x6C, };

__code unsigned char KEY_SET2_PAD8_MAKE[] = { 0x01, 0x75, };
__code unsigned char KEY_SET2_PAD8_BREAK[] = { 0x02, 0xF0, 0x75, };

__code unsigned char KEY_SET2_PAD9_MAKE[] = { 0x01, 0x7D, };
__code unsigned char KEY_SET2_PAD9_BREAK[] = { 0x02, 0xF0, 0x7D, };

__code unsigned char KEY_SET2_PAD0_MAKE[] = { 0x01, 0x70, };
__code unsigned char KEY_SET2_PAD0_BREAK[] = { 0x02, 0xF0, 0x70, };

__code unsigned char KEY_SET2_PADPERIOD_MAKE[] = { 0x01, 0x71, };
__code unsigned char KEY_SET2_PADPERIOD_BREAK[] = { 0x02, 0xF0, 0x71, };

__code unsigned char KEY_SET2_EURO2_MAKE[] = { 0x01, 0x61, };
__code unsigned char KEY_SET2_EURO2_BREAK[] = { 0x02, 0xF0, 0x61, };

__code unsigned char KEY_SET2_APP_MAKE[] = { 0x02, 0xE0, 0x2F, };
__code unsigned char KEY_SET2_APP_BREAK[] = { 0x03, 0xE0, 0xF0, 0x2F, };

__code unsigned char KEY_SET2_KEYPOWER_MAKE[] = { 0x02, 0xE0, 0x37, };
__code unsigned char KEY_SET2_KEYPOWER_BREAK[] = { 0x03, 0xE0, 0xF0, 0x37, };

__code unsigned char KEY_SET2_PADEQUALS_MAKE[] = { 0x01, 0x0F, };
__code unsigned char KEY_SET2_PADEQUALS_BREAK[] = { 0x02, 0xF0, 0x0F, };

__code unsigned char KEY_SET2_F13_MAKE[] = { 0x01, 0x08, };
__code unsigned char KEY_SET2_F13_BREAK[] = { 0x02, 0xF0, 0x08, };

__code unsigned char KEY_SET2_F14_MAKE[] = { 0x01, 0x10, };
__code unsigned char KEY_SET2_F14_BREAK[] = { 0x02, 0xF0, 0x10, };

__code unsigned char KEY_SET2_F15_MAKE[] = { 0x01, 0x18, };
__code unsigned char KEY_SET2_F15_BREAK[] = { 0x02, 0xF0, 0x18, };

__code unsigned char KEY_SET2_F16_MAKE[] = { 0x01, 0x20, };
__code unsigned char KEY_SET2_F16_BREAK[] = { 0x02, 0xF0, 0x20, };

__code unsigned char KEY_SET2_F17_MAKE[] = { 0x01, 0x28, };
__code unsigned char KEY_SET2_F17_BREAK[] = { 0x02, 0xF0, 0x28, };

__code unsigned char KEY_SET2_F18_MAKE[] = { 0x01, 0x30, };
__code unsigned char KEY_SET2_F18_BREAK[] = { 0x02, 0xF0, 0x30, };

__code unsigned char KEY_SET2_F19_MAKE[] = { 0x01, 0x38, };
__code unsigned char KEY_SET2_F19_BREAK[] = { 0x02, 0xF0, 0x38, };

__code unsigned char KEY_SET2_F20_MAKE[] = { 0x01, 0x40, };
__code unsigned char KEY_SET2_F20_BREAK[] = { 0x02, 0xF0, 0x40, };

__code unsigned char KEY_SET2_F21_MAKE[] = { 0x01, 0x48, };
__code unsigned char KEY_SET2_F21_BREAK[] = { 0x02, 0xF0, 0x48, };

__code unsigned char KEY_SET2_F22_MAKE[] = { 0x01, 0x50, };
__code unsigned char KEY_SET2_F22_BREAK[] = { 0x02, 0xF0, 0x50, };

__code unsigned char KEY_SET2_F23_MAKE[] = { 0x01, 0x57, };
__code unsigned char KEY_SET2_F23_BREAK[] = { 0x02, 0xF0, 0x57, };

__code unsigned char KEY_SET2_F24_MAKE[] = { 0x01, 0x5F, };
__code unsigned char KEY_SET2_F24_BREAK[] = { 0x02, 0xF0, 0x5F, };

__code unsigned char KEY_SET2_PADCOMMA_MAKE[] = { 0x01, 0x6D, };
__code unsigned char KEY_SET2_PADCOMMA_BREAK[] = { 0x02, 0xF0, 0x6D, };

__code unsigned char KEY_SET2_INTL1_MAKE[] = { 0x01, 0x51, };
__code unsigned char KEY_SET2_INTL1_BREAK[] = { 0x02, 0xF0, 0x51, };

__code unsigned char KEY_SET2_INTL2_MAKE[] = { 0x01, 0x13, };
__code unsigned char KEY_SET2_INTL2_BREAK[] = { 0x02, 0xF0, 0x13, };

__code unsigned char KEY_SET2_INTL3_MAKE[] = { 0x01, 0x6A, };
__code unsigned char KEY_SET2_INTL3_BREAK[] = { 0x02, 0xF0, 0x6A, };

__code unsigned char KEY_SET2_INTL4_MAKE[] = { 0x01, 0x64, };
__code unsigned char KEY_SET2_INTL4_BREAK[] = { 0x02, 0xF0, 0x64, };

__code unsigned char KEY_SET2_INTL5_MAKE[] = { 0x01, 0x67, };
__code unsigned char KEY_SET2_INTL5_BREAK[] = { 0x02, 0xF0, 0x67, };

__code unsigned char KEY_SET2_INTL6_MAKE[] = { 0x01, 0x27, };
__code unsigned char KEY_SET2_INTL6_BREAK[] = { 0x02, 0xF0, 0x27, };

__code unsigned char KEY_SET2_LANG1_MAKE[] = { 0x01, 0xF2, };
__code unsigned char KEY_SET2_LANG2_MAKE[] = { 0x01, 0xF1, };
__code unsigned char KEY_SET2_LANG3_MAKE[] = { 0x01, 0x63, };
__code unsigned char KEY_SET2_LANG3_BREAK[] = { 0x02, 0xF0, 0x63, };

__code unsigned char KEY_SET2_LANG4_MAKE[] = { 0x01, 0x62, };
__code unsigned char KEY_SET2_LANG4_BREAK[] = { 0x02, 0xF0, 0x62, };

__code unsigned char KEY_SET2_LANG5_MAKE[] = { 0x01, 0x5F, };
__code unsigned char KEY_SET2_LANG5_BREAK[] = { 0x02, 0xF0, 0x5F, };

__code unsigned char KEY_SET2_LCTRL_MAKE[] = { 0x01, 0x14, };
__code unsigned char KEY_SET2_LCTRL_BREAK[] = { 0x02, 0xF0, 0x14, };

__code unsigned char KEY_SET2_LSHIFT_MAKE[] = { 0x01, 0x12, };
__code unsigned char KEY_SET2_LSHIFT_BREAK[] = { 0x02, 0xF0, 0x12, };

__code unsigned char KEY_SET2_LALT_MAKE[] = { 0x01, 0x11, };
__code unsigned char KEY_SET2_LALT_BREAK[] = { 0x02, 0xF0, 0x11, };

__code unsigned char KEY_SET2_LGUI_MAKE[] = { 0x02, 0xE0, 0x1F, };
__code unsigned char KEY_SET2_LGUI_BREAK[] = { 0x03, 0xE0, 0xF0, 0x1F, };

__code unsigned char KEY_SET2_RCTRL_MAKE[] = { 0x02, 0xE0, 0x14, };
__code unsigned char KEY_SET2_RCTRL_BREAK[] = { 0x03, 0xE0, 0xF0, 0x14, };

__code unsigned char KEY_SET2_RSHIFT_MAKE[] = { 0x01, 0x59, };
__code unsigned char KEY_SET2_RSHIFT_BREAK[] = { 0x02, 0xF0, 0x59, };

__code unsigned char KEY_SET2_RALT_MAKE[] = { 0x02, 0xE0, 0x11, };
__code unsigned char KEY_SET2_RALT_BREAK[] = { 0x03, 0xE0, 0xF0, 0x11, };

__code unsigned char KEY_SET2_RGUI_MAKE[] = { 0x02, 0xE0, 0x27, };
__code unsigned char KEY_SET2_RGUI_BREAK[] = { 0x03, 0xE0, 0xF0, 0x27, };

__code unsigned char KEY_SET2_MEDIANEXT_MAKE[] = { 0x02, 0xE0, 0x4D, };
__code unsigned char KEY_SET2_MEDIANEXT_BREAK[] = { 0x03, 0xE0, 0xF0, 0x4D, };

__code unsigned char KEY_SET2_MEDIAPREV_MAKE[] = { 0x02, 0xE0, 0x15, };
__code unsigned char KEY_SET2_MEDIAPREV_BREAK[] = { 0x03, 0xE0, 0xF0, 0x15, };

__code unsigned char KEY_SET2_MEDIASTOP_MAKE[] = { 0x02, 0xE0, 0x3B, };
__code unsigned char KEY_SET2_MEDIASTOP_BREAK[] = { 0x03, 0xE0, 0xF0, 0x3B, };

__code unsigned char KEY_SET2_MEDIANPLAY_MAKE[] = { 0x02, 0xE0, 0x34, };
__code unsigned char KEY_SET2_MEDIANPLAY_BREAK[] = { 0x03, 0xE0, 0xF0, 0x34, };

__code unsigned char KEY_SET2_MEDIAMUTE_MAKE[] = { 0x02, 0xE0, 0x23, };
__code unsigned char KEY_SET2_MEDIAMUTE_BREAK[] = { 0x03, 0xE0, 0xF0, 0x23, };

__code unsigned char KEY_SET2_VOLUP_MAKE[] = { 0x02, 0xE0, 0x32, };
__code unsigned char KEY_SET2_VOLUP_BREAK[] = { 0x03, 0xE0, 0xF0, 0x32, };

__code unsigned char KEY_SET2_VOLDN_MAKE[] = { 0x02, 0xE0, 0x21, };
__code unsigned char KEY_SET2_VOLDN_BREAK[] = { 0x03, 0xE0, 0xF0, 0x21, };

__code unsigned char KEY_SET2_MEDSELECT_MAKE[] = { 0x02, 0xE0, 0x50, };
__code unsigned char KEY_SET2_MEDSELECT_BREAK[] = { 0x03, 0xE0, 0xF0, 0x50, };

__code unsigned char KEY_SET2_APPMAIL_MAKE[] = { 0x02, 0xE0, 0x48, };
__code unsigned char KEY_SET2_APPMAIL_BREAK[] = { 0x03, 0xE0, 0xF0, 0x48, };

__code unsigned char KEY_SET2_APPCALC_MAKE[] = { 0x02, 0xE0, 0x2B, };
__code unsigned char KEY_SET2_APPCALC_BREAK[] = { 0x03, 0xE0, 0xF0, 0x2B, };

__code unsigned char KEY_SET2_APPMYCOMP_MAKE[] = { 0x02, 0xE0, 0x40, };
__code unsigned char KEY_SET2_APPMYCOMP_BREAK[] = { 0x03, 0xE0, 0xF0, 0x40, };

__code unsigned char KEY_SET2_WWWSEARCH_MAKE[] = { 0x02, 0xE0, 0x10, };
__code unsigned char KEY_SET2_WWWSEARCH_BREAK[] = { 0x03, 0xE0, 0xF0, 0x10, };

__code unsigned char KEY_SET2_WWWHOME_MAKE[] = { 0x02, 0xE0, 0x3A, };
__code unsigned char KEY_SET2_WWWHOME_BREAK[] = { 0x03, 0xE0, 0xF0, 0x3A, };

__code unsigned char KEY_SET2_WWWBACK_MAKE[] = { 0x02, 0xE0, 0x38, };
__code unsigned char KEY_SET2_WWWBACK_BREAK[] = { 0x03, 0xE0, 0xF0, 0x38, };

__code unsigned char KEY_SET2_WWWFORWARD_MAKE[] = { 0x02, 0xE0, 0x30, };
__code unsigned char KEY_SET2_WWWFORWARD_BREAK[] = { 0x03, 0xE0, 0xF0, 0x30, };

__code unsigned char KEY_SET2_WWWSTOP_MAKE[] = { 0x02, 0xE0, 0x28, };
__code unsigned char KEY_SET2_WWWSTOP_BREAK[] = { 0x03, 0xE0, 0xF0, 0x28, };

__code unsigned char KEY_SET2_WWWREFRESH_MAKE[] = { 0x02, 0xE0, 0x20, };
__code unsigned char KEY_SET2_WWWREFRESH_BREAK[] = { 0x03, 0xE0, 0xF0, 0x20, };

__code unsigned char KEY_SET2_WWWFAVE_MAKE[] = { 0x02, 0xE0, 0x18, };
__code unsigned char KEY_SET2_WWWFAVE_BREAK[] = { 0x03, 0xE0, 0xF0, 0x18, };

const unsigned char * const HIDtoSET2_Make[] = {
NULL,
NULL,
NULL,
NULL,
KEY_SET2_A_MAKE,
KEY_SET2_B_MAKE,
KEY_SET2_C_MAKE,
KEY_SET2_D_MAKE,
KEY_SET2_E_MAKE,
KEY_SET2_F_MAKE,
KEY_SET2_G_MAKE,
KEY_SET2_H_MAKE,
KEY_SET2_I_MAKE,
KEY_SET2_J_MAKE,
KEY_SET2_K_MAKE,
KEY_SET2_L_MAKE,
KEY_SET2_M_MAKE,
KEY_SET2_N_MAKE,
KEY_SET2_O_MAKE,
KEY_SET2_P_MAKE,
KEY_SET2_Q_MAKE,
KEY_SET2_R_MAKE,
KEY_SET2_S_MAKE,
KEY_SET2_T_MAKE,
KEY_SET2_U_MAKE,
KEY_SET2_V_MAKE,
KEY_SET2_W_MAKE,
KEY_SET2_X_MAKE,
KEY_SET2_Y_MAKE,
KEY_SET2_Z_MAKE,
KEY_SET2_1_MAKE,
KEY_SET2_2_MAKE,
KEY_SET2_3_MAKE,
KEY_SET2_4_MAKE,
KEY_SET2_5_MAKE,
KEY_SET2_6_MAKE,
KEY_SET2_7_MAKE,
KEY_SET2_8_MAKE,
KEY_SET2_9_MAKE,
KEY_SET2_0_MAKE,
KEY_SET2_ENTER_MAKE,
KEY_SET2_ESCAPE_MAKE,
KEY_SET2_BKSPACE_MAKE,
KEY_SET2_TAB_MAKE,
KEY_SET2_SPACE_MAKE,
KEY_SET2_DASH_MAKE,
KEY_SET2_EQUALS_MAKE,
KEY_SET2_LEFTSQB_MAKE,
KEY_SET2_RIGHTSQB_MAKE,
KEY_SET2_BKSLASH_MAKE,
KEY_SET2_EURO1_MAKE,
KEY_SET2_SEMICOLON_MAKE,
KEY_SET2_APOSTROPHE_MAKE,
KEY_SET2_TILDE_MAKE,
KEY_SET2_COMMA_MAKE,
KEY_SET2_PERIOD_MAKE,
KEY_SET2_FWSLASH_MAKE,
KEY_SET2_CAPS_MAKE,
KEY_SET2_F1_MAKE,
KEY_SET2_F2_MAKE,
KEY_SET2_F3_MAKE,
KEY_SET2_F4_MAKE,
KEY_SET2_F5_MAKE,
KEY_SET2_F6_MAKE,
KEY_SET2_F7_MAKE,
KEY_SET2_F8_MAKE,
KEY_SET2_F9_MAKE,
KEY_SET2_F10_MAKE,
KEY_SET2_F11_MAKE,
KEY_SET2_F12_MAKE,
KEY_SET2_PRTSCR_MAKE,
KEY_SET2_SCRLOCK_MAKE,
KEY_SET2_PAUSE_MAKE,
KEY_SET2_INSERT_MAKE,
KEY_SET2_HOME_MAKE,
KEY_SET2_PGUP_MAKE,
KEY_SET2_DELETE_MAKE,
KEY_SET2_END_MAKE,
KEY_SET2_PGDN_MAKE,
KEY_SET2_RIGHT_MAKE,
KEY_SET2_LEFT_MAKE,
KEY_SET2_DOWN_MAKE,
KEY_SET2_UP_MAKE,
KEY_SET2_NUMLCK_MAKE,
KEY_SET2_PADFWSLASH_MAKE,
KEY_SET2_PADASTERISK_MAKE,
KEY_SET2_PADMINUS_MAKE,
KEY_SET2_PADPLUS_MAKE,
KEY_SET2_PADENTER_MAKE,
KEY_SET2_PAD1_MAKE,
KEY_SET2_PAD2_MAKE,
KEY_SET2_PAD3_MAKE,
KEY_SET2_PAD4_MAKE,
KEY_SET2_PAD5_MAKE,
KEY_SET2_PAD6_MAKE,
KEY_SET2_PAD7_MAKE,
KEY_SET2_PAD8_MAKE,
KEY_SET2_PAD9_MAKE,
KEY_SET2_PAD0_MAKE,
KEY_SET2_PADPERIOD_MAKE,
KEY_SET2_EURO2_MAKE,
KEY_SET2_APP_MAKE,
KEY_SET2_KEYPOWER_MAKE,
KEY_SET2_PADEQUALS_MAKE,
KEY_SET2_F13_MAKE,
KEY_SET2_F14_MAKE,
KEY_SET2_F15_MAKE,
KEY_SET2_F16_MAKE,
KEY_SET2_F17_MAKE,
KEY_SET2_F18_MAKE,
KEY_SET2_F19_MAKE,
KEY_SET2_F20_MAKE,
KEY_SET2_F21_MAKE,
KEY_SET2_F22_MAKE,
KEY_SET2_F23_MAKE,
KEY_SET2_F24_MAKE,
NULL,
NULL,
NULL,
NULL,
NULL,
NULL,
NULL,
NULL,
NULL,
NULL,
NULL,
NULL,
NULL,
NULL,
NULL,
NULL,
NULL,
KEY_SET2_PADCOMMA_MAKE,
NULL,
KEY_SET2_INTL1_MAKE,
KEY_SET2_INTL2_MAKE,
KEY_SET2_INTL3_MAKE,
KEY_SET2_INTL4_MAKE,
KEY_SET2_INTL5_MAKE,
KEY_SET2_INTL6_MAKE,
NULL,
NULL,
NULL,
KEY_SET2_LANG1_MAKE,
KEY_SET2_LANG2_MAKE,
KEY_SET2_LANG3_MAKE,
KEY_SET2_LANG4_MAKE,
KEY_SET2_LANG5_MAKE,
NULL,
NULL,
NULL,
NULL,
NULL,
NULL,
NULL,
NULL,
NULL,
NULL,
NULL,
NULL,
NULL,
NULL,
NULL,
NULL,
NULL,
NULL,
NULL,
NULL,
NULL,
NULL,
NULL,
NULL,
NULL,
NULL,
NULL,
NULL,
NULL,
NULL,
NULL,
NULL,
NULL,
NULL,
NULL,
NULL,
NULL,
NULL,
NULL,
NULL,
NULL,
NULL,
NULL,
NULL,
NULL,
NULL,
NULL,
NULL,
NULL,
NULL,
NULL,
NULL,
NULL,
NULL,
NULL,
NULL,
NULL,
NULL,
NULL,
NULL,
NULL,
NULL,
NULL,
NULL,
NULL,
NULL,
NULL,
NULL,
NULL,
NULL,
NULL,
NULL,
NULL,
NULL,
NULL,
KEY_SET2_LCTRL_MAKE,
KEY_SET2_LSHIFT_MAKE,
KEY_SET2_LALT_MAKE,
KEY_SET2_LGUI_MAKE,
KEY_SET2_RCTRL_MAKE,
KEY_SET2_RSHIFT_MAKE,
KEY_SET2_RALT_MAKE,
KEY_SET2_RGUI_MAKE,
NULL,
NULL,
NULL,
NULL,
NULL,
NULL,
NULL,
NULL,
NULL,
NULL,
NULL,
NULL,
NULL,
NULL,
NULL,
NULL,
NULL,
NULL,
NULL,
NULL,
NULL,
NULL,
NULL,
NULL,
};

const unsigned char * const HIDtoSET2_Break[] = {
NULL,
NULL,
NULL,
NULL,
KEY_SET2_A_BREAK,
KEY_SET2_B_BREAK,
KEY_SET2_C_BREAK,
KEY_SET2_D_BREAK,
KEY_SET2_E_BREAK,
KEY_SET2_F_BREAK,
KEY_SET2_G_BREAK,
KEY_SET2_H_BREAK,
KEY_SET2_I_BREAK,
KEY_SET2_J_BREAK,
KEY_SET2_K_BREAK,
KEY_SET2_L_BREAK,
KEY_SET2_M_BREAK,
KEY_SET2_N_BREAK,
KEY_SET2_O_BREAK,
KEY_SET2_P_BREAK,
KEY_SET2_Q_BREAK,
KEY_SET2_R_BREAK,
KEY_SET2_S_BREAK,
KEY_SET2_T_BREAK,
KEY_SET2_U_BREAK,
KEY_SET2_V_BREAK,
KEY_SET2_W_BREAK,
KEY_SET2_X_BREAK,
KEY_SET2_Y_BREAK,
KEY_SET2_Z_BREAK,
KEY_SET2_1_BREAK,
KEY_SET2_2_BREAK,
KEY_SET2_3_BREAK,
KEY_SET2_4_BREAK,
KEY_SET2_5_BREAK,
KEY_SET2_6_BREAK,
KEY_SET2_7_BREAK,
KEY_SET2_8_BREAK,
KEY_SET2_9_BREAK,
KEY_SET2_0_BREAK,
KEY_SET2_ENTER_BREAK,
KEY_SET2_ESCAPE_BREAK,
KEY_SET2_BKSPACE_BREAK,
KEY_SET2_TAB_BREAK,
KEY_SET2_SPACE_BREAK,
KEY_SET2_DASH_BREAK,
KEY_SET2_EQUALS_BREAK,
KEY_SET2_LEFTSQB_BREAK,
KEY_SET2_RIGHTSQB_BREAK,
KEY_SET2_BKSLASH_BREAK,
KEY_SET2_EURO1_BREAK,
KEY_SET2_SEMICOLON_BREAK,
KEY_SET2_APOSTROPHE_BREAK,
KEY_SET2_TILDE_BREAK,
KEY_SET2_COMMA_BREAK,
KEY_SET2_PERIOD_BREAK,
KEY_SET2_FWSLASH_BREAK,
KEY_SET2_CAPS_BREAK,
KEY_SET2_F1_BREAK,
KEY_SET2_F2_BREAK,
KEY_SET2_F3_BREAK,
KEY_SET2_F4_BREAK,
KEY_SET2_F5_BREAK,
KEY_SET2_F6_BREAK,
KEY_SET2_F7_BREAK,
KEY_SET2_F8_BREAK,
KEY_SET2_F9_BREAK,
KEY_SET2_F10_BREAK,
KEY_SET2_F11_BREAK,
KEY_SET2_F12_BREAK,
KEY_SET2_PRTSCR_BREAK,
KEY_SET2_SCRLOCK_BREAK,
NULL,
KEY_SET2_INSERT_BREAK,
KEY_SET2_HOME_BREAK,
KEY_SET2_PGUP_BREAK,
KEY_SET2_DELETE_BREAK,
KEY_SET2_END_BREAK,
KEY_SET2_PGDN_BREAK,
KEY_SET2_RIGHT_BREAK,
KEY_SET2_LEFT_BREAK,
KEY_SET2_DOWN_BREAK,
KEY_SET2_UP_BREAK,
KEY_SET2_NUMLCK_BREAK,
KEY_SET2_PADFWSLASH_BREAK,
KEY_SET2_PADASTERISK_BREAK,
KEY_SET2_PADMINUS_BREAK,
KEY_SET2_PADPLUS_BREAK,
KEY_SET2_PADENTER_BREAK,
KEY_SET2_PAD1_BREAK,
KEY_SET2_PAD2_BREAK,
KEY_SET2_PAD3_BREAK,
KEY_SET2_PAD4_BREAK,
KEY_SET2_PAD5_BREAK,
KEY_SET2_PAD6_BREAK,
KEY_SET2_PAD7_BREAK,
KEY_SET2_PAD8_BREAK,
KEY_SET2_PAD9_BREAK,
KEY_SET2_PAD0_BREAK,
KEY_SET2_PADPERIOD_BREAK,
KEY_SET2_EURO2_BREAK,
KEY_SET2_APP_BREAK,
KEY_SET2_KEYPOWER_BREAK,
KEY_SET2_PADEQUALS_BREAK,
KEY_SET2_F13_BREAK,
KEY_SET2_F14_BREAK,
KEY_SET2_F15_BREAK,
KEY_SET2_F16_BREAK,
KEY_SET2_F17_BREAK,
KEY_SET2_F18_BREAK,
KEY_SET2_F19_BREAK,
KEY_SET2_F20_BREAK,
KEY_SET2_F21_BREAK,
KEY_SET2_F22_BREAK,
KEY_SET2_F23_BREAK,
KEY_SET2_F24_BREAK,
NULL,
NULL,
NULL,
NULL,
NULL,
NULL,
NULL,
NULL,
NULL,
NULL,
NULL,
NULL,
NULL,
NULL,
NULL,
NULL,
NULL,
KEY_SET2_PADCOMMA_BREAK,
NULL,
KEY_SET2_INTL1_BREAK,
KEY_SET2_INTL2_BREAK,
KEY_SET2_INTL3_BREAK,
KEY_SET2_INTL4_BREAK,
KEY_SET2_INTL5_BREAK,
KEY_SET2_INTL6_BREAK,
NULL,
NULL,
NULL,
NULL,
NULL,
KEY_SET2_LANG3_BREAK,
KEY_SET2_LANG4_BREAK,
KEY_SET2_LANG5_BREAK,
NULL,
NULL,
NULL,
NULL,
NULL,
NULL,
NULL,
NULL,
NULL,
NULL,
NULL,
NULL,
NULL,
NULL,
NULL,
NULL,
NULL,
NULL,
NULL,
NULL,
NULL,
NULL,
NULL,
NULL,
NULL,
NULL,
NULL,
NULL,
NULL,
NULL,
NULL,
NULL,
NULL,
NULL,
NULL,
NULL,
NULL,
NULL,
NULL,
NULL,
NULL,
NULL,
NULL,
NULL,
NULL,
NULL,
NULL,
NULL,
NULL,
NULL,
NULL,
NULL,
NULL,
NULL,
NULL,
NULL,
NULL,
NULL,
NULL,
NULL,
NULL,
NULL,
NULL,
NULL,
NULL,
NULL,
NULL,
NULL,
NULL,
NULL,
NULL,
NULL,
NULL,
NULL,
NULL,
KEY_SET2_LCTRL_BREAK,
KEY_SET2_LSHIFT_BREAK,
KEY_SET2_LALT_BREAK,
KEY_SET2_LGUI_BREAK,
KEY_SET2_RCTRL_BREAK,
KEY_SET2_RSHIFT_BREAK,
KEY_SET2_RALT_BREAK,
KEY_SET2_RGUI_BREAK,
NULL,
NULL,
NULL,
NULL,
NULL,
NULL,
NULL,
NULL,
NULL,
NULL,
NULL,
NULL,
NULL,
NULL,
NULL,
NULL,
NULL,
NULL,
NULL,
NULL,
NULL,
NULL,
NULL,
NULL,
};
