proboterror/HIDman_ZX/firmware/uart1.c

/********************************** (C) COPYRIGHT *********** ********************
* File Name: UART1_Query.C
* Author: WCH
* Version: V1.3
* Date: 2016/06/24
* Description: Provides the configuration function of UART1, provides query mode for data transmission and reception, and the use of serial port FIFO.
                       Data receiving and sending
************************************************** *****************************/


#include "ch559.h"
#include "uart.h"

#define CH559UART1_FIFO_EN 1 //Enable CH559 serial port 1 receiving FIFO (receive and send 8 bytes each)

#if CH559UART1_FIFO_EN
UINT8 CH559UART1_FIFO_CNT = 0;
#define CH559UART1_FIFO_TRIG 7 // FIFO full 7 bytes trigger interrupt (1, 2, 4, or 7 bytes)
#endif

/************************************************* ******************************
* Function Name: ResetUART1()
* Description: CH559UART1 port soft reset
* Input: None
* Output: None
* Return: None
************************************************** *****************************/
void ResetUART1(void)
{
    SER1_IER |= bIER_RESET; //This bit can be automatically cleared to reset the serial port register
}

/************************************************* ******************************
* Function Name: CH559UART1Init(UINT8 DIV,UINT8 mode,UINT8 pin)
* Description: CH559 UART1 initialization setting
* Input:
                   UINT8 DIV sets the frequency division coefficient, clock frequency=Fsys/DIV, DIV cannot be 0
                   UINT8 mode, mode selection, 1: normal serial port mode; 0: 485 mode
                   UINT8 pin, serial port pin selection;
                   When mode=1
                   0: RXD1=P4.0, TXD1 is off;
                   1: RXD1&TXD1=P4.0&P4.4;
                   2: RXD1&TXD1=P2.6&P2.7;
                   3: RXD1&TXD1&TNOW=P2.6&P2.7&P2.5;
                   When mode=0
                   0: meaningless
                   1: Connect P5.4&P5.5 to 485, TNOW=P4.4;
                   2: P5.4&P5.5 connect to 485;
                   3: P5.4&P5.5 connect to 485, TNOW=P2.5;
                   UINT32 bps, transfer rate in baud
                   UINT8 databits, databits per word, must be 5, 6, 7 or 8
* Output: None
* Return: None
************************************************** *****************************/
void CH559UART1Init(UINT8 DIV,UINT8 mode,UINT8 pin,UINT32 bps,UINT8 databits)
{
    UINT32 x;
    UINT8 x2;

    SER1_LCR |= bLCR_DLAB; // DLAB bit is 1, write DLL, DLM and DIV registers
    SER1_DIV = DIV; // Prescaler
    x = 10 * FREQ_SYS *2 / DIV / 16 / bps;
    x2 = x% 10;
    x /= 10;
    if (x2 >= 5) x ++; //Rounding
    SER1_DLM = x>>8;
    SER1_DLL = x&0xff;
    SER1_LCR &= ~bLCR_DLAB; //DLAB bit is 0 to prevent modification of UART1 baud rate and clock
    if(mode == 1) //Close RS485 mode RS485_EN = 0, can not be omitted
    {
XBUS_AUX |= bALE_CLK_EN;
    }
    else if(mode == 0) //Enable RS485 mode RS485_EN = 1;
    {
UHUB1_CTRL |= bUH1_DISABLE;
PIN_FUNC &= ~bXBUS_CS_OE;
PIN_FUNC |= bXBUS_AL_OE;
XBUS_AUX &= ~bALE_CLK_EN;
SER1_MCR |= bMCR_HALF; //485 mode can only use half-duplex mode
    }
    SER1_LCR = (SER1_LCR & ~MASK_U1_WORD_SZ) | ((databits - 5) & MASK_U1_WORD_SZ); //Line control, 5, 6, 7 or 8 databits
    SER1_LCR &= ~(bLCR_PAR_EN | bLCR_STOP_BIT); //Wireless path interval, no parity, 1 stop bit

    SER1_MCR &= ~bMCR_TNOW;
    //SER1_IER |= bIER_EN_MODEM_O;
    SER1_IER |= ((pin << 4) & MASK_U1_PIN_MOD); //Serial port mode configuration
    //SER1_IER |= /*bIER_MODEM_CHG | bIER_LINE_STAT | bIER_THR_EMPTY | bIER_RECV_RD;//Interrupt enable configuration

#if CH559UART1_FIFO_EN
    SER1_FCR |= (MASK_U1_FIFO_TRIG & (CH559UART1_FIFO_TRIG << 5)) | bFCR_T_FIFO_CLR | bFCR_R_FIFO_CLR | bFCR_FIFO_EN;//FIFO controller
                                                                               //Empty the receive and transmit FIFO, 7-byte receive trigger, FIFO enable
#endif
    //SER1_MCR |= bMCR_OUT2; //MODEM control register
                                                                               //Interrupt request output, no actual interrupt
    SER1_ADDR |= 0xff; //Close multi-machine communication
}

/************************************************* ******************************
* Function Name: CH559UART1RcvByte()
* Description: CH559UART1 receives one byte
* Input: None
* Output: None
* Return: correct: UINT8 Rcvdat; receive data
************************************************** *****************************/
UINT8 CH559UART1RcvByte(void)
{
    while((SER1_LSR & bLSR_DATA_RDY) == 0); //Wait for the data to be ready
    return SER1_RBR;
}


#if CH559UART1_FIFO_EN
/************************************************* ******************************
* Function Name: CH559UART1Rcv(PUINT8 buf,UINT8 len)
* Description: CH559UART1 receives multiple bytes, FIFO must be opened
* Input: PUINT8 buf data storage buffer
                   UINT8 len Data pre-receive length
* Output: None
* Return: None
************************************************** *****************************/
void CH559UART1Rcv(PUINT8 buf,UINT8 len)
{
    UINT8 i,j;
    j = 0;
    while(len)
    {
         if(len >= CH559UART1_FIFO_TRIG)//The pre-receive length exceeds the FIFO receive trigger level
         {
             while((SER1_IIR & U1_INT_RECV_RDY) == 0);//Waiting for data available interrupt
             for(i=0;i<CH559UART1_FIFO_TRIG;i++)
             {
                 *(buf+j) = SER1_RBR;
                 j++;
             }
             len -= CH559UART1_FIFO_TRIG;
         }
         else
         {
             while((SER1_LSR & bLSR_DATA_RDY) == 0);//Wait for the data to be ready
             *(buf+j) = SER1_RBR;
             j++;
             len--;
         }
    }

}
#endif

/************************************************* ******************************
* Function Name: CH559UART1SendByte(UINT8 SendDat)
* Description: CH559UART1 sends one byte
* Input: UINT8 SendDat; the data to be sent
* Output: None
* Return: None
************************************************** *****************************/
void CH559UART1SendByte(UINT8 SendDat)
{
#if CH559UART1_FIFO_EN
    while(1)
    {
        if(SER1_LSR & bLSR_T_FIFO_EMP) CH559UART1_FIFO_CNT=8;//FIFO empty can fill up to 8 bytes
        if (CH559UART1_FIFO_CNT!=0)
        {
            SER1_THR = SendDat;
            CH559UART1_FIFO_CNT--;//FIFO count
            break;
        }
        while ((SER1_LSR & bLSR_T_FIFO_EMP) == 0 );//It is found that the FIFO is full and can only wait for the first 1 byte to be sent
    }
#else
    while ((SER1_LSR & bLSR_T_ALL_EMP) == 0 );//Do not open FIFO, wait for the completion of 1 byte transmission
    SER1_THR = SendDat;
#endif
}

/************************************************* ******************************
* Function Name: CH559UART1SendStr(PUINT8 SendStr)
* Description: CH559UART1 sends multiple bytes
* Input: UINT8 SendStr; the first address of the data to be sent
* Output: None
* Return: None
************************************************** *****************************/
void CH559UART1SendStr(PUINT8 SendStr)
{
#if CH559UART1_FIFO_EN
    while(1)
    {
        if(SER1_LSR & bLSR_T_FIFO_EMP) CH559UART1_FIFO_CNT=8;//FIFO empty can fill up to 8 bytes
        while( CH559UART1_FIFO_CNT!=0)
        {
            if( *SendStr =='\0') break;//Send is complete
            SER1_THR = *SendStr++;
            CH559UART1_FIFO_CNT--;//FIFO count

        }
        if( *SendStr =='\0') break;//Send is complete
        while ((SER1_LSR & bLSR_T_FIFO_EMP) == 0 );//It is found that the FIFO is full and can only wait for the first 1 byte to be sent
}
#else
    while( *SendStr !='\0')
    {
        while ((SER1_LSR & bLSR_T_ALL_EMP) == 0 );//Do not open FIFO, wait for the completion of 1 byte transmission
        SER1_THR = *SendStr++;
    }
#endif
}
