proboterror/HIDman_ZX/firmware/ps2_keyboard.c

#include <string.h>

#include "ps2_keyboard.h"

#include "ch559.h"
#include "type.h"
#include "system.h"
#include "gpio.h"
#include "keyboardled.h"

#define PS2_CLK_PORT 3
#define PS2_CLK_PIN 2
#define PS2_DATA_PORT 3
#define PS2_DATA_PIN 4

SBIT(PS2_KEY_CLOCK, PADR(PS2_CLK_PORT), PS2_CLK_PIN);
SBIT(PS2_KEY_DATA, PADR(PS2_DATA_PORT), PS2_DATA_PIN);

// Code originated from murmulator platform (https://murmulator.ru) PS/2 keyboard driver source code (drivers/ps2/ps2.c) with modifications.

// Keyboard input buffer can be changed from PS/2 INT0, USB interrupt and main loop.
// INT_NO_INT0 interrupt have higher priority (0) than USB interrupt INT_NO_USB (8),
// so interrupts should be disabled while changing buffer from USB interrupt handler and main loop.
volatile __data uint8_t ps2bufsize = 0;
volatile __data uint8_t ps2buffer[KBD_BUFFER_SIZE] /*= {}*/;

// Intended to call from USB interrupt.
// Warning: can break multi-byte PS/2 scancode transfer.
bool ps2_add_raw_code(const uint8_t *data)
{
	uint8_t len = *data;

	if(ps2bufsize + len >= KBD_BUFFER_SIZE)
		return false;

	EX0 = 0; // Disable PS/2 keyboard interrupt while changing keyboard input buffer.

	while(len--)
	{
		ps2buffer[ps2bufsize++] = *(++data);
	}

	EX0 = 1; // Enable PS/2 keyboard interupt.

	return true;
}

// Intended to call from main update loop.
uint8_t ps2_get_raw_code(uint8_t *code_0, uint8_t *code_1, uint8_t *code_2)
{
	uint8_t len = 0;

	if (!ps2bufsize)
		return 0;

	switch (ps2buffer[0])
	{
		case 0xF0: // Key with break(up) code: 0xF0, 0xXX
			len = 2;
		case 0xE0: // Extended key with code: 0xEX, 0xXX
		case 0xE1:
			len = 2;

			if(ps2bufsize > 1)
			{
				if(ps2buffer[1] == 0xF0) // Extended key with break(up) code: 0xEX, 0xF0, 0xXX
					len = 3;
			}
			break;
		default:
			len = 1;
			break;
	}

	if (ps2bufsize < len)
		return 0;

	setLED(false); // Turn off LED for a while

	*code_0 = ps2buffer[0];
	
	if (len > 1)
		*code_1 = ps2buffer[1];

	if (len > 2)
		*code_2 = ps2buffer[2];

	// Disable global interupts while changing keyboard input buffer.
	// Warning: Some memory accesses (especially XDATA) may rely on interrupt-driven banking schemes.
	// Disabling interrupts can break banked memory pointer access,
	// and lcall (long call) jumps to a function in banked memory (like _gptrget).
	E_DIS = 1;

	for (uint32_t i = len; i < KBD_BUFFER_SIZE; i++)
	{
		ps2buffer[i - len] = ps2buffer[i];
	}

	ps2bufsize -= len;

	E_DIS = 0; // Enable global interrupts.

	return len;
}

extern volatile uint32_t __data time_ms_32;

// See also PS2KeyRaw library: Arduino PS2 keyboard interface by Paul Carpenter
// https://github.com/techpaul/PS2KeyRaw
void ext0_interrupt(void) __interrupt(INT_NO_INT0)
{
	static __data uint8_t bitcount = 0;
	static __data uint8_t incoming = 0;
	static __data uint8_t parity;
	static __data uint32_t prev_ms = 0;

	const uint8_t val = PS2_KEY_DATA;

	if (time_ms_32 - prev_ms > 250) // 250 ms bit receive timeout.
	{
		bitcount = 0;
		incoming = 0;
	}

	prev_ms = time_ms_32;

	bitcount++;

	switch( bitcount )
	{
	case 1:  // Start bit
		incoming = 0;
		parity = 0;
		break;
	case 2:
	case 3:
	case 4:
	case 5:
	case 6:
	case 7:
	case 8:
	case 9: // Data bits
		parity += val;        // another one received ?
		incoming >>= 1;       // right shift one place for next bit
		incoming |= ( val ) ? 0x80 : 0;    // or in MSbit
		break;
	case 10: // Parity check
		parity &= 1;          // Get LSB if 1 = odd number of 1's so parity should be 0
		if( parity == val )   // Both same parity error
			parity = 0xFD;      // To ensure at next bit count clear and discard
		break;
	case 11: // Stop bit
		if( parity >= 0xFD )  // had parity error
		{
			// Should send resend byte command here currently discard
		}
		else                  // Good so save byte in buffer
		{
			// Assume USB interrupt have lower priority
			// and cannot preempt while changing keyboard buffer.
			if (ps2bufsize < KBD_BUFFER_SIZE)
			{
				ps2buffer[ps2bufsize++] = incoming;
			}
		}
		bitcount = 0;
		break;
	default: // in case of weird error and end of byte reception re-sync
		bitcount = 0;
	}
}

void ps2_keyboard_init(void)
{
	// Open drain output, no pull-up, support input
	pinMode(PS2_CLK_PORT, PS2_CLK_PIN, PIN_MODE_OUTPUT_OPEN_DRAIN);
	pinMode(PS2_DATA_PORT, PS2_DATA_PIN, PIN_MODE_OUTPUT_OPEN_DRAIN);

	PS2_KEY_CLOCK = PS2_KEY_DATA = 1;

	EX0 = 1; // enable external interrupt INT0 or LED interrupt
	IT0 = 1; // INT0 interrupt type: 0=low level action, 1=falling edge action

	memset(ps2buffer, 0, sizeof(ps2buffer));
}
