proboterror/HIDman_ZX/firmware/xbox360_usb.h

#pragma once

// XBox 360 Controller USB driver

#include <stdint.h>
#include <stdbool.h>

bool xbox360_usb_match(uint16_t vendor_id, uint16_t product_id);
bool xbox360_usb_init(USB_HUB_PORT *pUsbDevice, USB_CFG_DESCR *pCfgDescr, uint16_t len);
bool xbox360_usb_poll(USB_HUB_PORT *pUsbDevice, uint8_t* gamepad_state);
