proboterror/HIDman_ZX/firmware/data.h

#ifndef __DATA_H__
#define __DATA_H__
#include <stdbool.h>
#include <stdint.h>

#include "defs.h"

extern __code JoyPreset DefaultJoyMaps[];
extern __code JoyPreset KempstonJoyMaps[];

extern __xdata uint8_t StandardKeyboardDescriptor[];
extern __xdata uint8_t StandardMouseDescriptor[];
#endif
